tengigabytes/MokyaLora/docs/requirements/hardware-requirements.md

# Hardware Requirements Specification

**Project:** MokyaLora (Project MS-RP2350 — Meshtastic Feature Phone)
**Version:** v5.2

---

## 1. Core Compute

| Role | Part | Package | Notes |
|---|---|---|---|
| MCU | RP2350B | QFN-80 | Dual-core Cortex-M33, 1.8 V logic, no built-in flash |
| Flash | Winbond W25Q128JW | WSON-8 | 16 MB, 1.8 V, QSPI |
| PSRAM | AP Memory APS6404L-3SQN | QFN | 8 MB, 1.8 V, QSPI — holds IME Trie index and UI double-buffer at runtime |
| MCU Crystal | Abracon ABM8-272-T3 | SMD | 12.000 MHz |

**Design constraints:**
- QSPI Flash and PSRAM must be placed adjacent to MCU; 33 Ω series resistors on CLK lines.
- Expose QSPI Flash CS to a test point or micro switch — anti-brick: forces ROM bootloader (UF2 mode).
- Expose SWCLK, SWDIO, GND test points — required for dual-core AMP debugging with a hardware debugger.

---

## 2. Power System

### 2.1 Components

| Role | Part | Package | Notes |
|---|---|---|---|
| Charger / Path | TI BQ25622RYKR | DSBGA-18 | I2C, 16-bit ADC, VINDPM (solar MPPT), OTG 5 V boost; **no D+/D−** to preserve MCU USB signal integrity |
| Buck Inductor | Murata DFE322520F-1R5M | 3225 | 1.5 µH, metal-alloy shielded — lower ripple than 1.0 µH, better for RF-sensitive design |
| Fuel Gauge | TI BQ27441DRZR | SON-12 | Impedance Track™; must be in series with battery current path |
| 1.8 V Buck | TI TPS62840DLCR | VSON-8 | 60 nA Iq — minimises standby current |
| 3.3 V LDO | TI TPS7A2033 | WSON-6 | 300 mA, ultra-low noise (high PSRR) — clean supply for GPS/RF analogue |
| LED / BL Driver | TI LM27965 | WQFN-24 | Dual-bank I2C dimming (Power bus, `i2c1` on RP2350); Bank A = LCD BL, Bank B = keypad BL; HWEN tied to 1.8 V |
| Battery | Nokia BL-4C | — | Li-ion 3.7 V, ~890 mAh |
| Battery Connector | AVX 009155003301006 | 3-pin pogo | 2.5 mm pitch; polarity marked on silkscreen |

### 2.2 Power Rail Summary

| Rail | Voltage | Regulator | Key Loads |
|---|---|---|---|
| 1.8 V | 1.8 V | TPS62840 | MCU, Flash, PSRAM, SX1262 VDD_IN + VBAT_IO, Mic, LCD logic, GPS I/O |
| 3.3 V | 3.3 V | TPS7A2033 | **SX1262 VBAT (PA + Rx)**, GPS RF, LCD analogue, magnetometer, barometer |
| VSYS | ~3.5–4.2 V | BQ25622 | Buck input, LDO input, audio amp, backlight, motor |
| OTG | 5 V | BQ25622 boost | USB VBUS reverse power output |

See `docs/design-notes/power-architecture.md` for the full power tree.

**Design constraints:**
- Charger ILIM: hardware resistor sets 500 mA default; MCU raises limit to 1–2 A via I2C after USB enumeration.
- BQ25622 PMID bulk capacitor must be placed close to IC; VBUS trace rated for ≥ 2 A.
- BQ27441 SRX–VSS sense path must be short and wide (in series with battery current loop).
- TPS7A2033 EN pin tied to VSYS / 1.8 V (always-on).

---

## 3. RF — LoRa

### 3.1 Components

| Role | Part | Package | Notes |
|---|---|---|---|
| LoRa Transceiver | Semtech SX1262 | QFN-24 | SPI1; supports 150–960 MHz sub-GHz bands |
| TCXO | ECS-TXO-20CSMV4-320-AY-TR | SMD | 32 MHz, 1.8 V, ±0.5 ppm, clipped sine output |
| RF Switch | Murata PE4259 | SPDT | Tx / Rx antenna path switching |
| LoRa Antenna | Kyocera AVX M620720 | Chip | Placed at top PCB edge |
| RF Shield | Wurth 3600213120S | SMT frame + lid | Covers digital core to reduce radiated emissions |

### 3.2 SPI1 Interface

| Signal | Notes |
|---|---|
| LORA_MISO  | SPI1 |
| LORA_nCS | SPI1 chip select |
| LORA_SCK | SPI1 |
| LORA_MOSI  | SPI1 |
| LORA_BUSY  | Active-high; poll before each SPI transaction |
| LORA_DIO1  | IRQ / DORMANT wakeup source |
| LORA_nRST  | Active-low reset |

GPIO assignments: see `docs/design-notes/mcu-gpio-allocation.md`.

**Design constraints:**
- RF traces: 50 Ω controlled impedance on dedicated RF layer.
- TCXO XTA pin: 220 Ω series resistor + 10 pF shunt capacitor — mandatory per Semtech application note.
- U.FL test connector on RF signal path for bench RF matching and power verification.

---

## 4. RF — GNSS

### 4.1 Components

| Role | Part | Package | Notes |
|---|---|---|---|
| GNSS Receiver | ST Teseo-LIV3FL | LGA-14 | Multi-constellation; I2C1 (Sensor + GNSS bus), address 0x3A |
| LNA | Infineon BGA123N6 | — | GPS/GNSS LNA; 1.8 V VPON enable |
| SAW Filter | Qualcomm B39162B4327P810 | — | L1 bandpass, after LNA |
| GNSS Antenna | Kyocera AVX M830120 | Chip | Placed at left PCB edge |

**Design constraints:**
- Protocol Select pin must be configured for I2C mode.
- RF trace: 50 Ω controlled impedance.
- 3.3 V supply (TPS7A2033) for RF and analogue sections.
- SDA/SCL share sensor bus pull-ups with other sensors.
- **MCU interface is I2C only** — Teseo `nRST` is **not** routed to any MCU GPIO on Rev A. Firmware can only issue software reset via `$PSTMCOLDSTART` / `$PSTMSRR` proprietary commands over I2C; a hard reset requires power cycling the 3.3 V rail.

---

## 5. Display

### 5.1 Components

| Role | Part | Package | Notes |
|---|---|---|---|
| LCD | Newhaven NHD-2.4-240320AF | — | 2.4″ IPS, 240×320, 8-bit parallel 8080, no touch |
| FPC Connector | Molex 54132-4062 | FPC-40 | 0.5 mm pitch ZIF, 40-pin |

### 5.2 Interface

| Signal | Notes |
|---|---|
| TFT_nCS | Chip select |
| TFT_DCX | Data / command select |
| TFT_nWR | Write strobe |
| TFT_D8–D15 | 8-bit parallel data bus (PIO) |
| TFT_nRST | Reset |
| TFT_TE | Tearing effect |
| Backlight  | LM27965 Bank A, Power-bus I2C dimming |

GPIO assignments: see `docs/design-notes/mcu-gpio-allocation.md`.

**Design constraints:**
- FPC connector: insert FPC with contacts facing **down**; verify orientation before locking ZIF.

---

## 6. Audio

### 6.1 Components

| Role | Part | Package | Notes |
|---|---|---|---|
| Microphone | Infineon IM69D130 | LGA-5 | PDM, SNR 69 dB, AOP 128 dBSPL; bottom-port |
| Audio Amplifier | Nuvoton NAU8315YG | WSON-6 | 3.2 W Class-D I2S |
| Speaker | CUI CMS-131304-SMT-TR | SMT | 0.7 W, 8 Ω |

### 6.2 Interface

| Signal | Notes |
|---|---|
| MIC_CLK  | PDM clock output to mic |
| MIC_DATA | PDM data input from mic |
| AMP_BCLK | I2S bit clock to amp |
| AMP_FSR  | I2S frame sync to amp |
| AMP_DAC  | I2S data output to amp |

GPIO assignments: see `docs/design-notes/mcu-gpio-allocation.md`.

**Design constraints:**
- IM69D130 is a bottom-port microphone: PCB must have an acoustic opening aligned to the mic inlet; enclosure must seal the acoustic cavity with a rubber gasket.
- NAU8315 software must limit output to −3 dB to protect the speaker from over-drive.

---

## 7. Sensors

### 7.1 Components

| Role | Part | Package | I2C1 Address | Address Setting |
|---|---|---|---|---|
| IMU (ACC + GYRO) | ST LSM6DSV16X | LGA-14 | 0x6A | SA0 → GND (default 0x6B conflicts with charger on the other bus) |
| Magnetometer | ST LIS2MDL | LGA-12 | 0x1E | Fixed |
| Barometer | ST LPS22HH | LGA-10 | 0x5D | SA0 → 3.3 V (Rev A confirmed; schematic ties SA0 to 3.3 V) |

All sensors share the **sensor + GNSS bus (GPIO 34 / 35)** with the Teseo-LIV3FL GNSS receiver. The Power bus (GPIO 6 / 7) and the Sensor + GNSS bus both map to the `i2c1` SDK peripheral on RP2350 (no I2C0 pinmux alternative exists on either pin pair); Rev A firmware time-multiplexes `i2c1` between the two pin pairs via a FreeRTOS mutex. Rev B should reroute the sensor + GNSS bus to a mod-4 = 0/1 GPIO pair to restore two independent SDK peripherals — see `docs/design-notes/mcu-gpio-allocation.md` for details.

**Design constraints:**
- LSM6DSV16X SA0 must be tied to GND — default address 0x6B would collide with BQ25622 if both were on the same bus.
- LPS22HH SA0 is tied to 3.3 V → address 0x5D (confirmed Rev A bring-up).
- I2C1 pull-ups: 2.2 kΩ–4.7 kΩ to 1.8 V on SDA and SCL.

---

## 8. Human Interface

### 8.1 Keypad

| Role | Part | Notes |
|---|---|---|
| Keypad Switches | SWT0105 | Metal dome sheet |
| Anti-ghost Diodes | Diodes Inc. SDM03U40 | SOD-523 Schottky, Vf ~0.37 V @ 30 mA; enables NKRO at 1.8 V logic |
| Keypad BL LEDs | LiteOn LTST-C191TBWET (×6–8) | White; driven by LM27965 Bank B (Power bus, `i2c1` on RP2350) |

**Scan mechanism:** RP2350 PIO drives 6 column lines, samples 6 row lines. DMA writes key state directly to RAM — zero CPU overhead. Logic level 1.8 V, active-low. GPIO assignments: see `docs/design-notes/mcu-gpio-allocation.md`.

#### Physical Layout (6×6 Matrix)

```
[ Navigation & Control Area ]

      (Left)        (D-Pad)        (Right)      (Vol)
    +--------+    +    +    +    +--------+  +--------+
    |  FUNC  |    |    ▲    |    |   SET  |  |  VOL+  |
    +--------+    +    |    +    +--------+  +--------+
                  +--+ | +--+
             ◄ -- |  | OK |  | -- ►
                  +--+ | +--+
    +--------+    +    |    +    +--------+  +--------+
    |  BACK  |    |    ▼    |    |   DEL  |  |  VOL-  |
    +--------+    +    +    +    +--------+  +--------+

[ Core Input Area (5×5) ]

       Col 0       Col 1       Col 2       Col 3       Col 4
    +-------+   +-------+   +-------+   +-------+   +-------+
 R0 | 1 2   |   | 3 4   |   | 5 6   |   | 7 8   |   | 9 0   |
    | ㄅㄉ  |   | ˇˋ    |   | ㄓˊ   |   | ˙ㄚ   |   | ㄞㄢㄦ |
    | [ANS] |   | [7]   |   | [8]   |   | [9]   |   | [÷]   |
    +-------+   +-------+   +-------+   +-------+   +-------+
 R1 | Q W   |   | E R   |   | T Y   |   | U I   |   | O P   |
    | ㄆㄊ  |   | ㄍㄐ  |   | ㄔㄗ  |   | ㄧㄛ  |   | ㄟㄣ  |
    | [(]   |   | [4]   |   | [5]   |   | [6]   |   | [×]   |
    +-------+   +-------+   +-------+   +-------+   +-------+
 R2 | A S   |   | D F   |   | G H   |   | J K   |   |   L   |
    | ㄇㄋ  |   | ㄎㄑ  |   | ㄕㄘ  |   | ㄨㄜ  |   | ㄠㄤ  |
    | [)]   |   | [1]   |   | [2]   |   | [3]   |   | [-]   |
    +-------+   +-------+   +-------+   +-------+   +-------+
 R3 | Z X   |   | C V   |   | B N   |   |   M   |   |  ---  |
    | ㄈㄌ  |   | ㄏㄒ  |   | ㄖㄙ  |   | ㄩㄝ  |   | ㄡㄥ  |
    | [AC]  |   | [0]   |   | [.]   |   | [x10ˣ]|   | [+]   |
    +-------+   +-------+   +-------+   +-------+   +-------+
 R4 | MODE  |   |  TAB  |   | SPACE |   | ，SYM |   | 。.？ |
    +-------+   +-------+   +-------+   +-------+   +-------+
```

#### Electrical Matrix Map

| Row \ Col | Col 0 | Col 1 | Col 2 | Col 3 | Col 4 | Col 5 (ext) |
|---|---|---|---|---|---|---|
| Row 0 | 1 2 / ㄅㄉ / ANS | 3 4 / ˇˋ / 7 | 5 6 / ㄓˊ / 8 | 7 8 / ˙ㄚ / 9 | 9 0 / ㄞㄢ / ÷ | FUNC |
| Row 1 | Q W / ㄆㄊ / ( | E R / ㄍㄐ / 4 | T Y / ㄔㄗ / 5 | U I / ㄧㄛ / 6 | O P / ㄟㄣ / × | SET |
| Row 2 | A S / ㄇㄋ / ) | D F / ㄎㄑ / 1 | G H / ㄕㄘ / 2 | J K / ㄨㄜ / 3 | L / ㄠㄤ / - | BACK |
| Row 3 | Z X / ㄈㄌ / AC | C V / ㄏㄒ / 0 | B N / ㄖㄙ / . | M / ㄩㄝ / x10ˣ | — / ㄡㄥ / + | DEL |
| Row 4 | MODE | TAB | SPACE | ，SYM | 。.？ | VOL+ |
| Row 5 (nav) | UP | DOWN | LEFT | RIGHT | OK | VOL− |

> **Rev A bringup note:** The schematic SW designators are numbered column-major (SW1–6 = logical Col 5 ext top-to-bottom, i.e. FUNC/SET/BACK/DEL/VOL+/VOL−, then SW7–12 = Col 0 number row, etc.). As a result, the firmware GPIO scan index `(r, c)` does **not** correspond to the logical Row/Col above. See `docs/bringup/rev-a-bringup-log.md` Step 6 for the confirmed firmware `key_names[r][c]` table. Correct SW-to-Row/Col assignment should be verified against the schematic before Rev B firmware development.

### 8.2 Indicators & Haptics

| Role | Part | Notes |
|---|---|---|
| Status LED | LiteOn LTST-C235KGKRKT | Side-view, red/green; driven via LM27965 remaining channels; 256-step I2C dimming |
| Vibration Motor | HD-EMB1104-SM-2 | SMD ERM, 3 V, 80 mA |
| Motor MOSFET | Toshiba SSM3K56ACT | N-ch, low Vth, 1.8 V logic compatible, CST3; low-side driver |
| Motor Protection | Flyback diode | Reverse-parallel across motor terminals to absorb back-EMF |

**Design constraints:**
- 1.8 V GPIO rule: never drive LEDs or high-Vth MOSFETs directly from GPIO. Use SSM3K56ACT (low-Vth).
  - LED: common-anode to VSYS / 3.3 V; cathode through resistor to Drain; 100 kΩ pull-down on Gate.
  - Motor: low-side drive; motor+ to VSYS (5–10 Ω series); motor− to Drain.
- Flyback diode reverse-parallel across motor terminals is mandatory.

---

## 9. Connectivity — USB-C

| Role | Part | Package | Notes |
|---|---|---|---|
| USB-C Connector | GCT USB4105-GF-A | 16-pin mid-mount | Through-hole shell legs must be soldered for mechanical retention |

**Design constraints:**
- CC1 and CC2 must each have an **independent** 5.1 kΩ pull-down to GND — enables PD charger 5 V output.
- D+/D− connected to MCU only — not to charger IC (preserves USB signal integrity).
- ESD protection devices on D+/D− and VBUS.
- VBUS trace rated for ≥ 2 A.

---

## 10. I2C Bus Allocation

Bus assignments, 7-bit addresses, GPIO pin pairs, pull-up values, and the
RP2350 SDK peripheral note all live in
`docs/design-notes/mcu-gpio-allocation.md` to keep a single source of truth.

---

## 11. Mandatory Design Rules

1. **Anti-brick boot point:** expose QSPI Flash CS to a test point or micro switch — allows ROM bootloader entry when software is bricked.
2. **SWD debug interface:** expose SWCLK, SWDIO, GND — required for dual-core AMP debugging.
3. **1.8 V GPIO rule:** never drive LEDs or high-Vth MOSFETs directly. Use SSM3K56ACT (low-Vth) as switch.
   - LED: common-anode to VSYS / 3.3 V; cathode through resistor to Drain; 100 kΩ pull-down on Gate.
   - Motor: low-side drive; motor+ to VSYS (5–10 Ω series); motor− to Drain.
4. **OTG wiring:** BQ25622 PMID bulk capacitor must be close to IC; VBUS trace rated for ≥ 2 A.
5. **Fuel gauge path:** BQ27441 SRX–VSS sense path in battery current loop; trace must be short and wide.
6. **Acoustic seal:** IM69D130 is bottom-port; PCB must have an opening aligned to mic inlet; enclosure must seal with a rubber gasket.
7. **Signal integrity:** QSPI CLK lines need 33 Ω series resistors; Flash and PSRAM placed adjacent to MCU.
8. **Motor protection:** flyback diode reverse-parallel across motor terminals is mandatory.
9. **GPS I2C mode:** Teseo-LIV3FL Protocol Select pin must be configured for I2C mode.
10. **USB-C CC pins:** CC1 and CC2 must each have an independent 5.1 kΩ pull-down to GND to enable PD charger 5 V output.

---

## 12. Rev B Changes (Planned)

Changes based on Rev A bringup findings:

| Change | Reason | Priority | Reference |
|---|---|---|---|
| **TPS7A2033 EN → GPIO** | Gate 3.3 V rail in deepest DORMANT (PWR_BTN only, no LoRa) | **Critical** | Power review §8.4 |
| **Load switch on non-LoRa 3.3 V loads** | Isolate Teseo/LCD/sensors from SX1262 VBAT in STANDBY; SX1262 VBAT stays powered | **High** | Power review §8.4 |
| **Add NAND Flash** | Non-volatile storage (maps, message DB, OTA) | **High** | New requirement |
| **Remove NAU8315 amp + CMS-131304 speaker** | Audio not needed | High | User decision |
| **Remove IM69D130 PDM mic** | Audio not needed | High | User decision |
| **LM27965 HWEN → GPIO** | Full LED driver shutdown in DORMANT; saves ~5 µA | Medium | Power review §8.4 |
| Fix LIS2MDL I2C routing (SCL/SDA swap) | Issue 3 | High | Bringup log |
| Fix LPS22HH I2C routing + SA0 net | Issue 4 | High | Bringup log |
| Fix LCD FPC pinout | Issue 5 | High | Bringup log |
| Move D37 LED to LM27965 Bank A | Issue 6 | Medium | Bringup log |
| BQ25622 nCE → GND | Issue 2 | High | Bringup log |
| PSRAM GPIO 0 pull-up (4.7–10 kΩ) | Issue 8 | Medium | Bringup log |
| Consider I2C Bus B pull-up load switch | Protect against BQ27441 latchup drain (Issue 10) | Low | Power review §8.4 |

### NAND Flash (TBD)

- **Part:** TBD — select SPI NAND for minimal GPIO usage (shares SPI bus or dedicated CS)
- **Interface:** SPI or QSPI
- **Capacity:** TBD (512 MB–2 GB range typical for maps + message DB)
- **Power:** verify standby current; must support CE# deassert or Deep Power Down for low-power mode
- **Use cases:** offline vector maps, message history database, firmware OTA staging, large asset storage
- **Flash memory map impact:** LittleFS partition on NOR Flash (W25Q128JW) may be reduced or eliminated if NAND takes over user data storage; NOR retains firmware + MIE dictionary
