tengigabytes/MokyaLora/docs/bringup/mie-v4-status.md

# MIE v4 Composition Architecture — Status

Last updated: 2026-04-24

## Overview

The MokyaInput Engine has been refactored to **v4 Composition Architecture** to
solve three independent problems found via SWD+RTT latency profiling:

1. **Performance**: v2 `TrieSearcher::search` did O(words × 50) dedup linear
   scan over PSRAM — 580 ms worst case for common Bopomofo initials (ㄅ ㄉ).
2. **Coverage**: v2 dict had only 1,479 single chars reachable as 1-syllable
   IME input; users couldn't type many CJK chars.
3. **Ranking**: Same dict held all word lengths competing by freq, so 4-char
   成語 were perpetually ranked below higher-freq 2-char compounds.

## Architecture (one-paragraph summary)

A single `dict_mie.bin` (MIE4 magic) holds:
- `char_table`: 18,722 unique chars × per-char readings (key bytes + tone + freq)
- `word_table`: 128,855 multi-char words as `char_id[N]` sequences with
  per-position `reading_idx[N]` overrides for 多音字
- `first_char_idx`: per char_id → freq-sorted word_id list
- `key_to_char_idx`: per phoneme-key byte → candidate char_ids
- `char_offsets` / `word_offsets`: pre-computed u32 offsets into char_table /
  word_table (zero-heap embedded loader)

`CompositionSearcher::search(user_keys, n, target_char_count, ...)` walks
`key_to_char_idx[user_keys[0]]` → candidate chars → `first_char_idx[cid]` →
word_ids → `composition_matches` recursive backtracker over each char's
designated reading. **No abbreviation pre-computation in the dict** — search-
time composition derives all valid prefix patterns from char readings.

`ImeLogic::run_search_v4()` dispatches by `count_positions(key_seq_)`:
- 1-position → `search_chars` (char_table, not word_table group 1)
- 2-4 position → `target_char_count = positions` + adjacent-bucket fallback
- 5+ position → **char-by-char mode**: 1-char candidates for first initial
  (commit consumes 1 byte) + appended 5+ phrase matches as bonus

## Completed (Phase 0-5, Phase 1.4 A/B/C)

| Phase | Item | Status |
|---|---|---|
| 1.4 A | Long-press multitap cycling (short=fuzzy, long×N = primary/secondary/tertiary, mod phoneme_count) | ✅ 2026-04-24 |
| 1.4 A | Dict phoneme_pos byte (+1 % size) + `CompositionSearcher` hint filter | ✅ |
| 1.4 A | Engine `lp_cycle_` FSM + KeyEvent.flags + keypad_scan deferred press + 2-byte inject ring | ✅ |
| 1.4 B | SYM1 long-press 4×4 symbol picker (「」『』（）【】，。、；：？！…) | ✅ 2026-04-24 |
| 1.4 C | Idle OK = newline (mirrors idle SPACE = " ") | ✅ 2026-04-24 |
| 1.4 | 150 host unit tests green | ✅ |
| 1.4 | 6-passage SWD regression: 1 416 CJK / 100 % top-100 / 0 miss + 136/136 picker punct + 21/21 newlines + 48/48 spaces | ✅ |
| 0 | PoC simulation script (`scripts/poc_mie_v4_simulation.py`) | ✅ |
| 0 | Validation: dict ≤ 2.5 MB, ref-search p50 ≤ 5 ms | ✅ |
| 1 | `gen_dict.py` MIED v4 builder (parallel `--v4-output` flag) | ✅ |
| 1 | v4 binary format with embedded offset sections | ✅ |
| 1 | `verify_mied_v4.py` round-trip parser | ✅ |
| 2 | `CompositionSearcher` C++ class (header + impl + 8 tests) | ✅ |
| 2 | Backtracking `composition_matches` for abbreviation derivation | ✅ |
| 2 | `search_chars` for 1-char results from char_table | ✅ |
| 2 | Heap-free embedded loader (offsets read from file, not built) | ✅ |
| 3 | Position counter (H2 heuristic) in `ime_keys.cpp` | ✅ |
| 3 | `ImeLogic::run_search_v4` with bucket dispatch + fallback chains | ✅ |
| 3 | 5+ char-by-char mode | ✅ |
| 3 | `attach_composition_searcher` API (back-compat with v2 path) | ✅ |
| 4 | `test_position_counter.cpp` (16 tests) | ✅ |
| 4 | `test_composition_searcher.cpp` (8 tests) | ✅ |
| 4 | `test_ime_v4_dispatch.cpp` (4 tests incl. real-dict smoke) | ✅ |
| 4 | All 123 PC tests green | ✅ |
| 5 | `mie_dict_loader.c` v4 magic auto-detection + load path | ✅ |
| 5 | `ime_task.cpp` conditional CompositionSearcher attach | ✅ |
| 5 | `scripts/build_and_flash.sh --v4` flag | ✅ |
| 5 | Hardware boot + RTT measurement (initial run) | ✅ |
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
