tengigabytes/MokyaLora/hardware/kicad/BtryChrgr.kicad_sch

## KiCad design hardware/kicad/BtryChrgr.kicad_sch (2026-03-22)

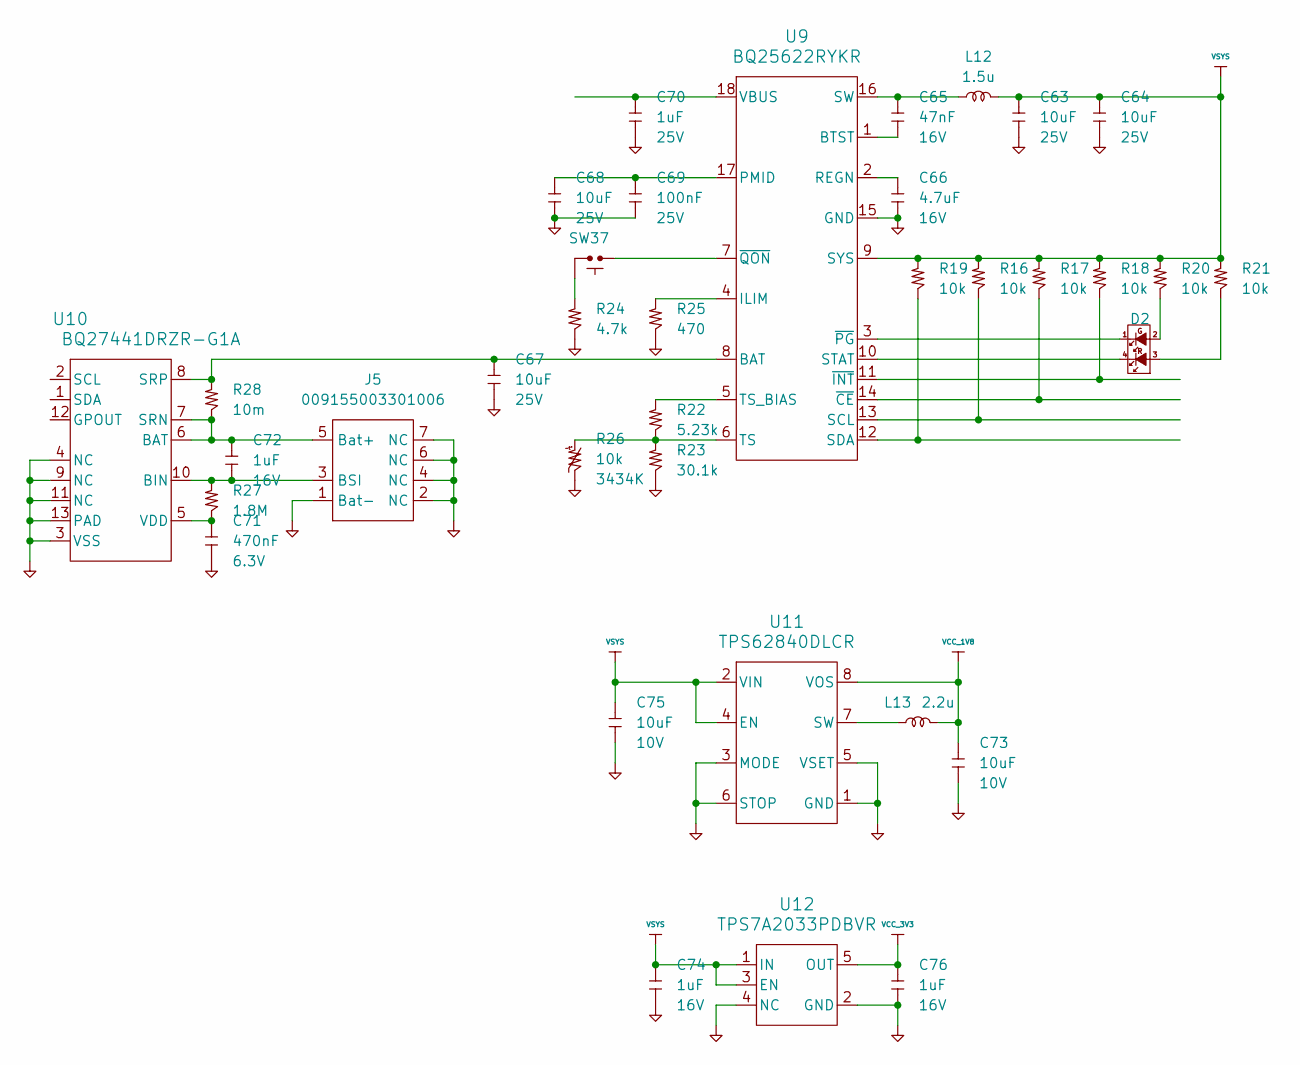
[picture p15: schematic BtryChrgr.kicad_sch]

Parts:
C63, C64, C67, C68: 10uF; C_1206_3216; Voltage 25V; MPN CC1206KKX7R8BB106
C65: 47nF; C_0402_1005; Voltage 16V; MPN AC0402KPX7R7BB473
C66: 4.7uF; C_0805_2012; Voltage 16V; MPN AC0805KKX7R7BB475
C69: 100nF; C_0402_1005; Voltage 25V; MPN AC0402KRX7R8BB104
C70: 1uF; C_1206_3216; Voltage 25V; MPN CC1206JKX7R8BB105
C71: 470nF; C_0402_1005; Voltage 6.3V; MPN AC0402KRX5R5BB474
C72, C74, C76: 1uF; C_0603_1608; Voltage 16V; MPN AC0603KRX7R7BB105
C73, C75: 10uF; C_0603_1608; Voltage 10V; MPN CC0603KRX5R6BB106
D2: LTST-C235KGKRKT; LED_LiteOn_LTST-C235KGKRKT
J5: 009155003301006; Mouser Part Number 581-009155003301006
L12: 1.5u; L_1210_3225; MPN DFE322520F-1R5M
L13: 2.2u; L_0806_2016; MPN DFE201612E-2R2M=P2
R16, R17, R18, R19, R20, R21: 10k; R_0402_1005; MPN AC0402FR-7W10KL
R22: 5.23k; R_0402_1005; MPN AC0402FR-075K23L
R23: 30.1k; R_0402_1005; MPN AC0402FR-0730K1L
R24: 4.7k; R_0402_1005; MPN AC0402FR-7W4K7L
R25: 470; R_0402_1005; MPN AC0402FR-7W470RL
R26: 10k; R_0402_1005; MPN NCU15XH103FBSRC
R27: 1.8M; R_0402_1005; MPN AC0402FR-071M8L
R28: 10m; R_0805_2012; MPN PA0805FRE470R01L
SW37: SWT0105-003516JSA; SWT0105
U9: BQ25622RYKR; WQFN-HR18__RYK_TEX; MPN BQ25622RYKR
U10: BQ27441DRZR-G1A; DRZ0012A
U11: TPS62840DLCR; VSON8_2P1X1P6_TEX
U12: TPS7A2033PDBVR; DBV0005A-IPC_C; MPN TPS7A2033PDBVR

Connections:
GND: C63.2, C64.2, C66.2, C67.2, C68.2, C69.2, C70.2, C71.2, C73.2, C74.2, C75.2, C76.2, J5.1 (Bat-), J5.2 (NC), J5.4 (NC), J5.6 (NC), J5.7 (NC), R23.2, R24.2, R25.2, R26.2, U9.15 (GND), U10.3 (VSS), U10.4 (NC), U10.9 (NC), U10.11 (NC), U10.13 (PAD), U11.1 (GND), U11.3 (MODE), U11.5 (VSET), U11.6 (STOP), U12.2 (GND), U12.4 (NC)
unnamed: C65.1, L12.1, U9.16 (SW)
unnamed: C65.2, U9.1 (BTST)
unnamed: C66.1, U9.2 (REGN)
unnamed: C67.1, R28.1, U9.8 (BAT), U10.8 (SRP)
unnamed: C68.1, C69.1, U9.17 (PMID)
unnamed: C70.1, U9.18 (VBUS)
unnamed: C71.1, R27.2, U10.5 (VDD)
unnamed: C72.1, J5.5 (Bat+), R28.2, U10.6 (BAT), U10.7 (SRN)
unnamed: C72.2, J5.3 (BSI), R27.1, U10.10 (BIN)
unnamed: D2.1 (K2), U9.3 (~PG)
unnamed: D2.2 (A2), R20.2
unnamed: D2.3 (A1), R21.2
unnamed: D2.4 (K1), U9.10 (STAT)
unnamed: L13.1, U11.7 (SW)
unnamed: R16.2, U9.13 (SCL)
unnamed: R17.2, U9.14 (~CE)
unnamed: R18.2, U9.11 (~INT)
unnamed: R19.2, U9.12 (SDA)
unnamed: R22.1, U9.5 (TS_BIAS)
unnamed: R22.2, R23.1, R26.1, U9.6 (TS)
unnamed: R24.1, SW37.1, SW37.2
unnamed: R25.1, U9.4 (ILIM)
unnamed: SW37.3, SW37.4, U9.7 (~QON)
VCC_1V8: C73.1, L13.2, U11.8 (VOS)
VCC_3V3: C76.1, U12.5 (OUT)
VSYS: C63.1, C64.1, C74.1, C75.1, L12.2, R16.1, R17.1, R18.1, R19.1, R20.1, R21.1, U9.9 (SYS), U11.2 (VIN), U11.4 (EN), U12.1 (IN), U12.3 (EN)
