tengigabytes/MokyaLora/hardware/kicad/Display.kicad_sch

## KiCad design hardware/kicad/Display.kicad_sch (2026-04-07)

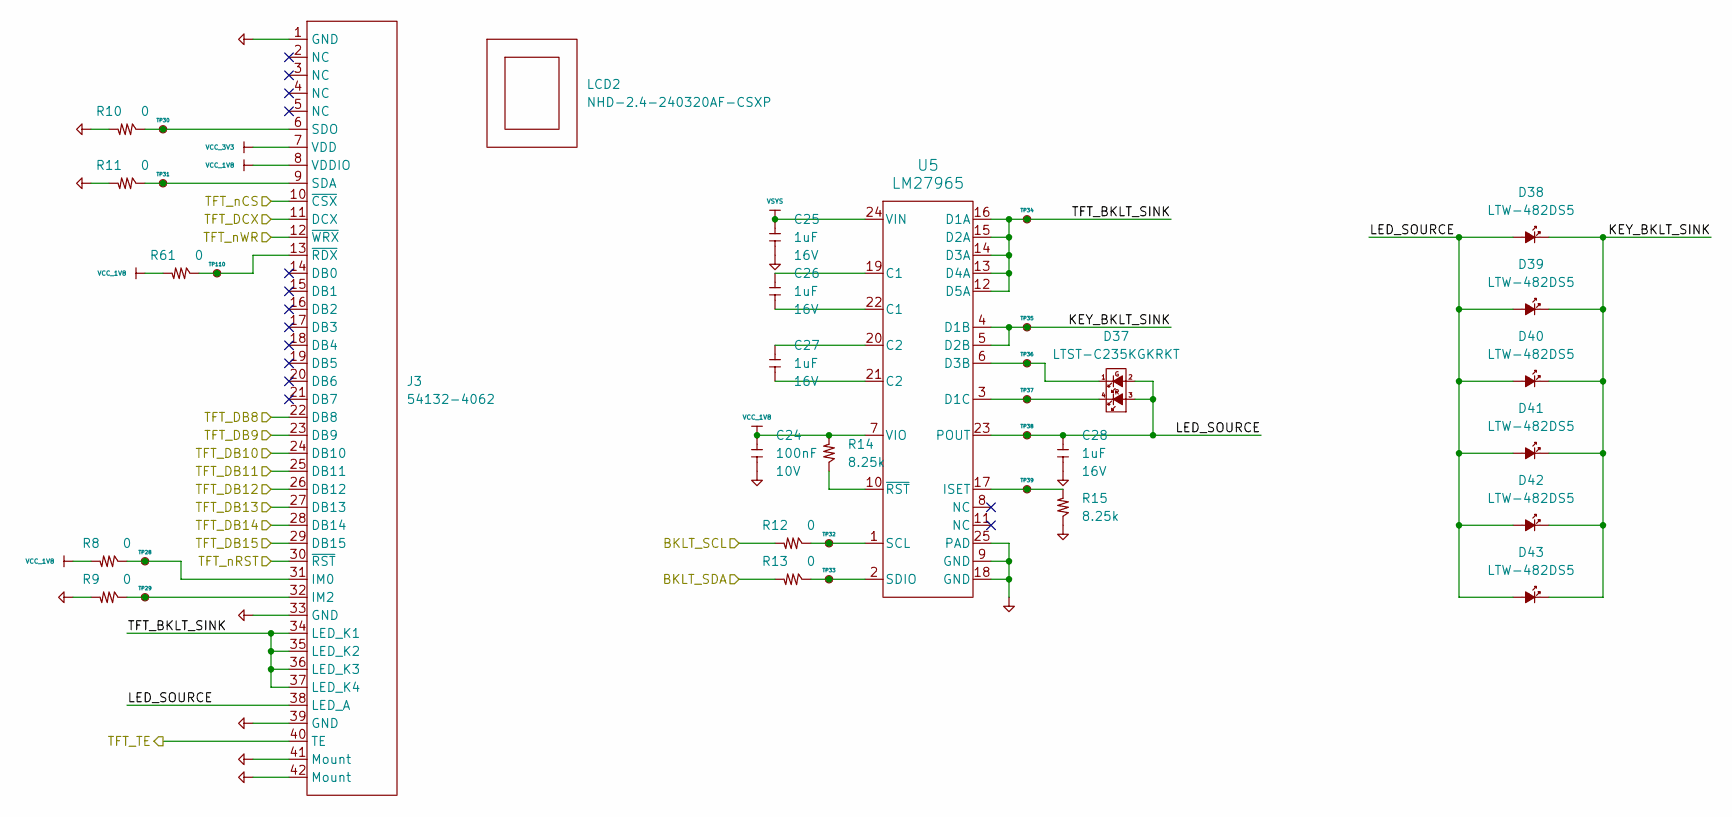
[picture p16: schematic Display.kicad_sch]

Parts:
C24: 100nF; C_0402_1005; Voltage 10V; MPN AC0402KRX7R6BB104; LCSC C3830899
C25, C26, C27, C28: 1uF; C_0603_1608; Voltage 16V; MPN AC0603KRX7R7BB105; LCSC C3905328
D37: LTST-C235KGKRKT; LED_LiteOn_LTST-C235KGKRKT; MPN LTST-C235KGKRKT; LCSC C125110
D38, D39, D40, D41, D42, D43: LTW-482DS5; MPN LTW-482DS5; LCSC C284930
J3: 54132-4062; 54132-4062_1; Mouser Part Number 538-54132-4062
LCD2: NHD-2.4-240320AF-CSXP; MPN NHD-2.4-240320AF-CSXP
R8, R9, R10, R11, R12, R13, R61: 0; R_0402_1005; MPN AC0402FR-070RL; LCSC C226739
R14, R15: 8.25k; R_0402_1005; MPN AC0402FR-078K25L; LCSC C227259
TP28, TP29, TP30, TP31, TP32, TP33, TP34, TP35, TP36, TP37, TP38, TP39, TP110: TestPoint_Small; TestPoint_Pad_D1.0mm; MPN test point
U5: LM27965; SQA24A; MPN LM27965SQ; LCSC C2679390

Connections:
BKLT_SCL: R12.1
BKLT_SDA: R13.1
GND: C24.2, C25.2, C28.2, J3.1 (GND), J3.33 (GND), J3.39 (GND), J3.41 (Mount), J3.42 (Mount), R9.1, R10.1, R11.1, R15.2, U5.9 (GND), U5.18 (GND), U5.25 (PAD)
KEY_BKLT_SINK: D38.C, D39.C, D40.C, D41.C, D42.C, D43.C, TP35.1, U5.4 (D1B), U5.5 (D2B)
LED_SOURCE: C28.1, D37.2 (A2), D37.3 (A1), D38.A, D39.A, D40.A, D41.A, D42.A, D43.A, J3.38 (LED_A), TP38.1, U5.23 (POUT)
unnamed: C26.1, U5.19 (C1)
unnamed: C26.2, U5.22 (C1)
unnamed: C27.1, U5.20 (C2)
unnamed: C27.2, U5.21 (C2)
unnamed: D37.1 (K2), TP36.1, U5.6 (D3B)
unnamed: D37.4 (K1), TP37.1, U5.3 (D1C)
unnamed: J3.6 (SDO), R10.2, TP30.1
unnamed: J3.9 (SDA), R11.2, TP31.1
unnamed: J3.13 (~RDX), R61.2, TP110.1
unnamed: J3.31 (IM0), R8.2, TP28.1
unnamed: J3.32 (IM2), R9.2, TP29.1
unnamed: R12.2, TP32.1, U5.1 (SCL)
unnamed: R13.2, TP33.1, U5.2 (SDIO)
unnamed: R14.2, U5.10 (~RST)
unnamed: R15.1, TP39.1, U5.17 (ISET)
TFT_BKLT_SINK: J3.34 (LED_K1), J3.35 (LED_K2), J3.36 (LED_K3), J3.37 (LED_K4), TP34.1, U5.12 (D5A), U5.13 (D4A), U5.14 (D3A), U5.15 (D2A), U5.16 (D1A)
TFT_DB8: J3.22 (DB8)
TFT_DB9: J3.23 (DB9)
TFT_DB10: J3.24 (DB10)
TFT_DB11: J3.25 (DB11)
TFT_DB12: J3.26 (DB12)
TFT_DB13: J3.27 (DB13)
TFT_DB14: J3.28 (DB14)
TFT_DB15: J3.29 (DB15)
TFT_DCX: J3.11 (DCX)
TFT_TE: J3.40 (TE)
TFT_nCS: J3.10 (~CSX)
TFT_nRST: J3.30 (~RST)
TFT_nWR: J3.12 (~WRX)
VCC_1V8: C24.1, J3.8 (VDDIO), R8.1, R14.1, R61.1, U5.7 (VIO)
VCC_3V3: J3.7 (VDD)
VSYS: C25.1, U5.24 (VIN)
