tengigabytes/MokyaLora/hardware/kicad/GNSS.kicad_sch

## KiCad design hardware/kicad/GNSS.kicad_sch (2026-04-07)

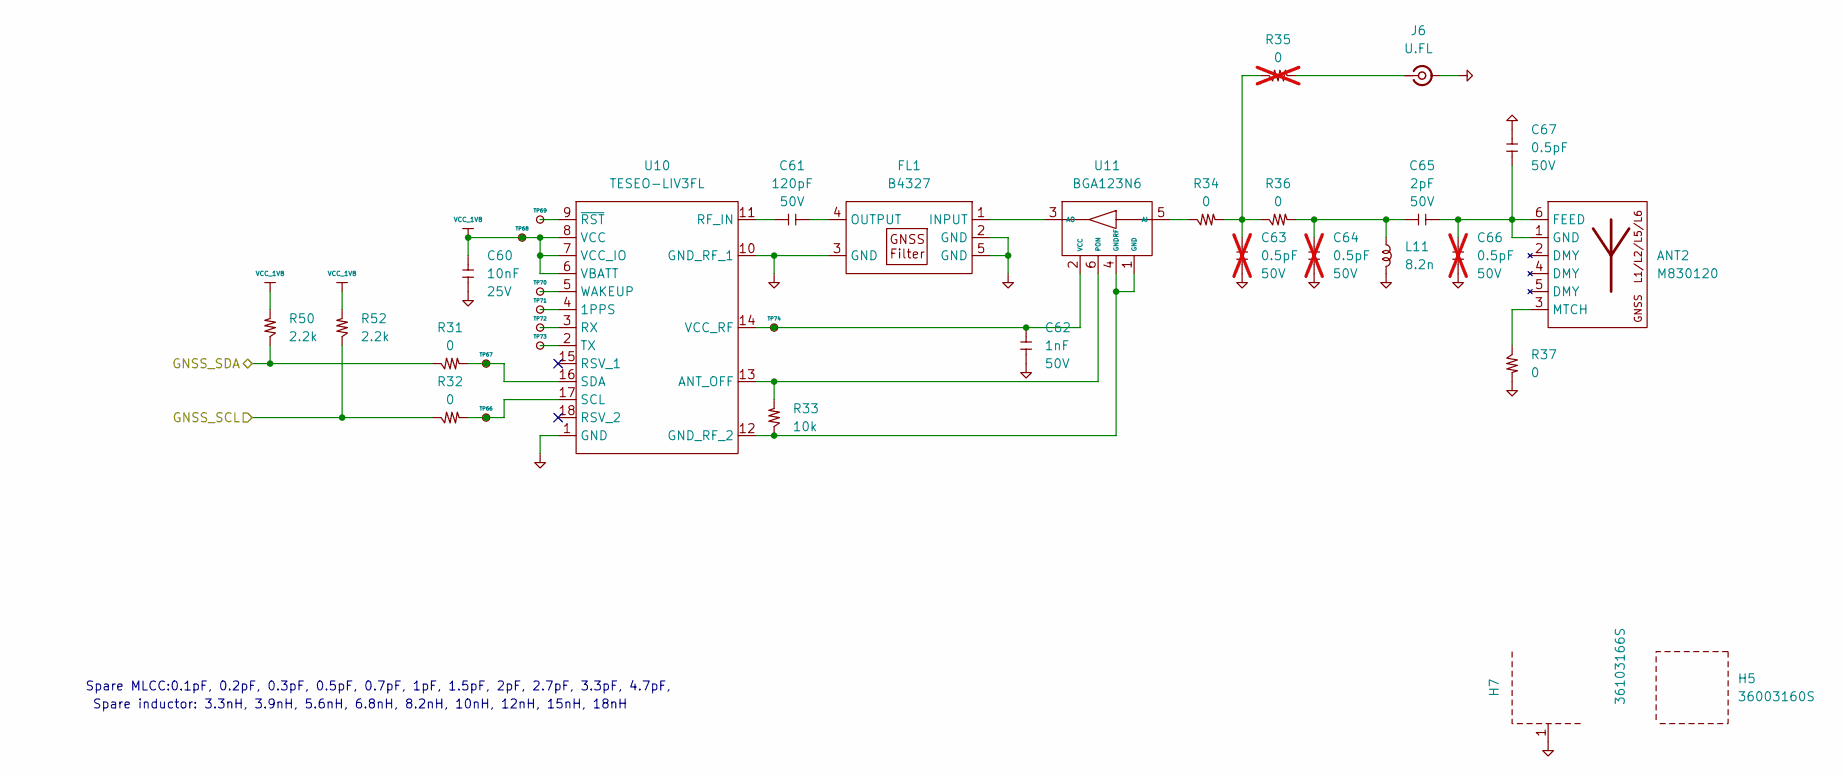
[picture p17: schematic GNSS.kicad_sch]

Parts:
ANT2: M830120; SON225P300X800X143-6N; Mouser Part Number 581-M830120
C60: 10nF; C_0402_1005; Voltage 25V; MPN AC0402KRX7R8BB103; LCSC C726521
C61: 120pF; C_0402_1005; Voltage 50V; MPN AC0402FRNPO9BN121; LCSC C6117687
C62: 1nF; C_0402_1005; Voltage 50V; MPN AC0402JRX7R9BB102; LCSC C726132
C63, C64, C66: 0.5pF; C_0402_1005; Voltage 50V; MPN AC0402BRNPO9BNR50; LCSC C2188174; not fitted
C65: 2pF; C_0402_1005; Voltage 50V; MPN AC0402BRNPO9BN2R0; LCSC C726106
C67: 0.5pF; C_0402_1005; Voltage 50V; MPN AC0402BRNPO9BNR50; LCSC C2188174
FL1: B4327; B39162B4327P810; Mouser Part Number 871-B39162B4327P810
H5: 36003160S; MPN 36003160S
H7: 36103166S; Part Number 36103166S; LCSC C7464147
J6: U.FL; U.FL_Hirose_U.FL-R-SMT-1_Vertical; MPN U.FL-R-SMT-1; LCSC C88374
L11: 8.2n; L_0402_1005; MPN LQW15AN8N2G80D; LCSC C307610
R31, R32, R34, R36, R37: 0; R_0402_1005; MPN AC0402FR-070RL; LCSC C226739
R33: 10k; R_0402_1005; MPN AC0402FR-7W10KL; LCSC C850723
R35: 0; R_0402_1005; MPN AC0402FR-070RL; LCSC C226739; not fitted
R50, R52: 2.2k; R_0402_1005; MPN AC0402FR-072K2L
TP66, TP67, TP68, TP69, TP70, TP71, TP72, TP73, TP74: TestPoint_Small; TestPoint_Pad_D1.0mm; MPN test point
U10: TESEO-LIV3FL; TESEOLIV3FL; Mouser Part Number 511-TESEO-LIV3FL
U11: BGA123N6; BGA725L6E6327; MPN BGA123N6E6327XTSA1; LCSC C3191830

Connections:
GND: C60.2, C62.2, C63.2, C64.2, C66.2, C67.1, FL1.2 (GND), FL1.3 (GND), FL1.5 (GND), H7.1, J6.2 (Ext), L11.2, R37.1, U10.1 (GND), U10.10 (GND_RF_1)
GNSS_SCL: R32.2, R52.2
GNSS_SDA: R31.2, R50.2
unnamed: ANT2.1 (GND), ANT2.6 (FEED), C65.2, C66.1, C67.2
unnamed: ANT2.3 (MTCH), R37.2
unnamed: C61.1, U10.11 (RF_IN)
unnamed: C61.2, FL1.4 (OUTPUT)
unnamed: C62.1, TP74.1, U10.14 (VCC_RF), U11.2 (VCC)
unnamed: C63.1, R34.1, R35.2, R36.2
unnamed: C64.1, C65.1, L11.1, R36.1
unnamed: FL1.1 (INPUT), U11.3 (AO)
unnamed: J6.1 (In), R35.1
unnamed: R31.1, TP67.1, U10.16 (SDA)
unnamed: R32.1, TP66.1, U10.17 (SCL)
unnamed: R33.1, U10.13 (ANT_OFF), U11.6 (PON)
unnamed: R33.2, U10.12 (GND_RF_2), U11.1 (GND), U11.4 (GNDRF)
unnamed: R34.2, U11.5 (AI)
unnamed: TP69.1, U10.9 (~RST)
unnamed: TP70.1, U10.5 (WAKEUP)
unnamed: TP71.1, U10.4 (1PPS)
unnamed: TP72.1, U10.3 (RX)
unnamed: TP73.1, U10.2 (TX)
VCC_1V8: C60.1, R50.1, R52.1, TP68.1, U10.6 (VBATT), U10.7 (VCC_IO), U10.8 (VCC)

Notes on the sheet:
Spare inductor: 3.3nH, 3.9nH, 5.6nH, 6.8nH, 8.2nH, 10nH, 12nH, 15nH, 18nH
Spare MLCC:0.1pF, 0.2pF, 0.3pF, 0.5pF, 0.7pF, 1pF, 1.5pF, 2pF, 2.7pF, 3.3pF, 4.7pF,
