tengigabytes/MokyaLora/hardware/kicad/IMU.kicad_sch

## KiCad design hardware/kicad/IMU.kicad_sch (2026-04-07)

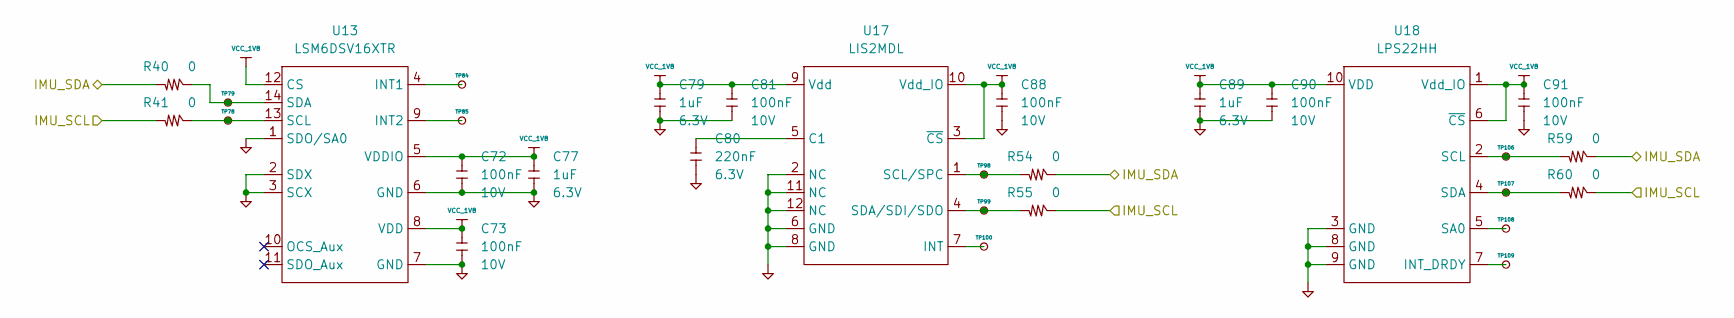
[picture p18: schematic IMU.kicad_sch]

Parts:
C72, C73, C81, C88, C90, C91: 100nF; C_0402_1005; Voltage 10V; MPN AC0402KRX7R6BB104; LCSC C3830899
C77, C79, C89: 1uF; C_0402_1005; Voltage 6.3V; MPN AC0402KRX5R5BB105; LCSC C3873469
C80: 220nF; C_0402_1005; Voltage 6.3V; MPN AC0402KRX5R5BB224; LCSC C3845337
R40, R41, R54, R55, R59, R60: 0; R_0402_1005; MPN AC0402FR-070RL; LCSC C226739
TP78, TP79, TP84, TP85, TP98, TP99, TP100, TP106, TP107, TP108, TP109: TestPoint_Small; TestPoint_Pad_D1.0mm; MPN test point
U13: LSM6DSV16XTR; LGA-14_3x2.5mm_P0.5mm_LayoutBorder3x4y; MPN LSM6DSV16XTR; LCSC C5267406
U17: LIS2MDL; LGA-12_2x2mm_P0.5mm; MPN LIS2MDL; LCSC C919695
U18: LPS22HH; ST_HLGA-10_2x2mm_P0.5mm_LayoutBorder3x2y; MPN LPS22HH; LCSC C2827824

Connections:
GND: C72.2, C73.2, C77.2, C79.2, C80.2, C81.2, C88.2, C89.2, C90.2, C91.2, U13.1 (SDO/SA0), U13.2 (SDX), U13.3 (SCX), U13.6 (GND), U13.7 (GND), U17.2 (NC), U17.6 (GND), U17.8 (GND), U17.11 (NC), U17.12 (NC), U18.3 (GND), U18.8 (GND), U18.9 (GND)
IMU_SCL: R41.1, R55.2, R60.2
IMU_SDA: R40.1, R54.2, R59.2
unnamed: C80.1, U17.5 (C1)
unnamed: R40.2, TP79.1, U13.14 (SDA)
unnamed: R41.2, TP78.1, U13.13 (SCL)
unnamed: R54.1, TP98.1, U17.1 (SCL/SPC)
unnamed: R55.1, TP99.1, U17.4 (SDA/SDI/SDO)
unnamed: R59.1, TP106.1, U18.2 (SCL)
unnamed: R60.1, TP107.1, U18.4 (SDA)
unnamed: TP84.1, U13.4 (INT1)
unnamed: TP85.1, U13.9 (INT2)
unnamed: TP100.1, U17.7 (DRDY)
unnamed: TP108.1, U18.5 (SA0)
unnamed: TP109.1, U18.7 (INT_DRDY)
VCC_1V8: C72.1, C73.1, C77.1, C79.1, C81.1, C88.1, C89.1, C90.1, C91.1, U13.5 (VDDIO), U13.8 (VDD), U13.12 (CS), U17.3 (~CS), U17.9 (Vdd), U17.10 (Vdd_IO), U18.1 (Vdd_IO), U18.6 (~CS), U18.10 (VDD)
