tengigabytes/MokyaLora/hardware/kicad/KeyBoard.kicad_sch

## KiCad design hardware/kicad/KeyBoard.kicad_sch (2026-04-07)

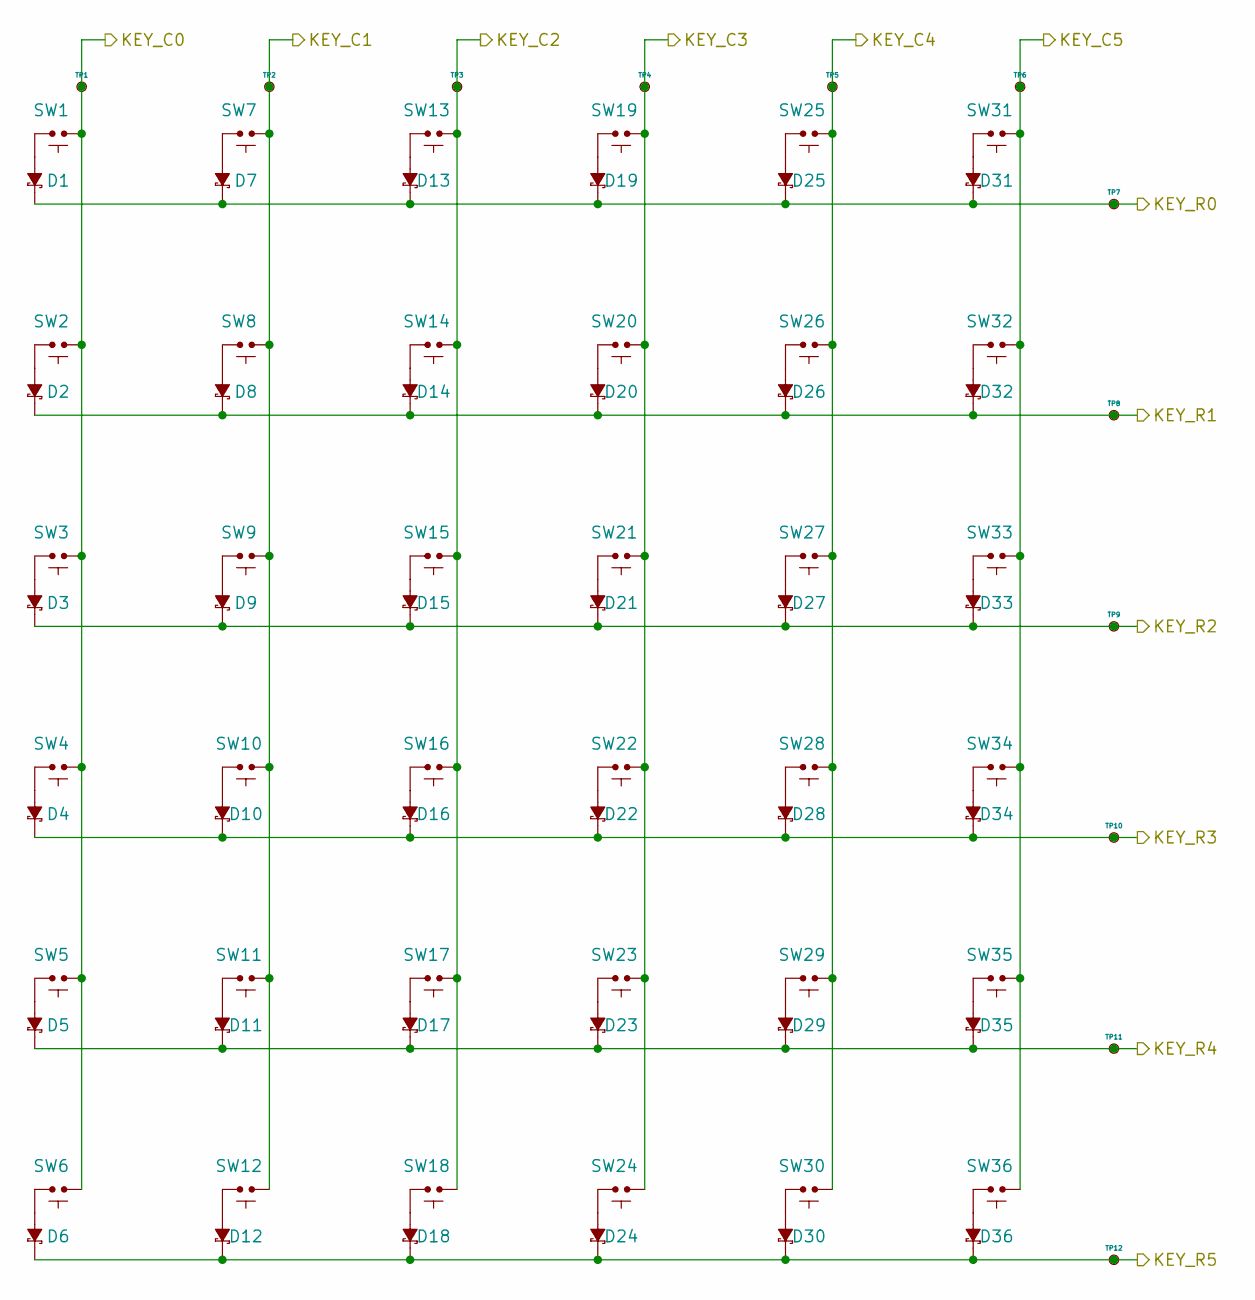
[picture p19: schematic KeyBoard.kicad_sch]

Parts:
D1, D2, D3, D4, D5, D6, D7, D8, D9, D10, D11, D12, D13, D14, D15, D16, D17, D18, D19, D20, D21, D22, D23, D24, D25, D26, D27, D28, D29, D30, D31, D32, D33, D34, D35, D36: D_SOD-523; MPN SDM03U40; LCSC C151333
SW1, SW2, SW3, SW4, SW5, SW6, SW7, SW8, SW9, SW10, SW11, SW12, SW13, SW14, SW15, SW16, SW17, SW18, SW19, SW20, SW21, SW22, SW23, SW24, SW25, SW26, SW27, SW28, SW29, SW30, SW31, SW32, SW33, SW34, SW35, SW36: SWT0105-003516JSA; SWT0105; MPN SWT0105-003516JSA
TP1, TP2, TP3, TP4, TP5, TP6, TP7, TP8, TP9, TP10, TP11, TP12: TestPoint_Small; TestPoint_Pad_D1.0mm; MPN test point

Connections:
KEY_C0: SW1.3, SW1.4, SW2.3, SW2.4, SW3.3, SW3.4, SW4.3, SW4.4, SW5.3, SW5.4, SW6.3, SW6.4, TP1.1
KEY_C1: SW7.3, SW7.4, SW8.3, SW8.4, SW9.3, SW9.4, SW10.3, SW10.4, SW11.3, SW11.4, SW12.3, SW12.4, TP2.1
KEY_C2: SW13.3, SW13.4, SW14.3, SW14.4, SW15.3, SW15.4, SW16.3, SW16.4, SW17.3, SW17.4, SW18.3, SW18.4, TP3.1
KEY_C3: SW19.3, SW19.4, SW20.3, SW20.4, SW21.3, SW21.4, SW22.3, SW22.4, SW23.3, SW23.4, SW24.3, SW24.4, TP4.1
KEY_C4: SW25.3, SW25.4, SW26.3, SW26.4, SW27.3, SW27.4, SW28.3, SW28.4, SW29.3, SW29.4, SW30.3, SW30.4, TP5.1
KEY_C5: SW31.3, SW31.4, SW32.3, SW32.4, SW33.3, SW33.4, SW34.3, SW34.4, SW35.3, SW35.4, SW36.3, SW36.4, TP6.1
KEY_R0: D1.C, D7.C, D13.C, D19.C, D25.C, D31.C, TP7.1
KEY_R1: D2.C, D8.C, D14.C, D20.C, D26.C, D32.C, TP8.1
KEY_R2: D3.C, D9.C, D15.C, D21.C, D27.C, D33.C, TP9.1
KEY_R3: D4.C, D10.C, D16.C, D22.C, D28.C, D34.C, TP10.1
KEY_R4: D5.C, D11.C, D17.C, D23.C, D29.C, D35.C, TP11.1
KEY_R5: D6.C, D12.C, D18.C, D24.C, D30.C, D36.C, TP12.1
unnamed: D1.A, SW1.1, SW1.2
unnamed: D2.A, SW2.1, SW2.2
unnamed: D3.A, SW3.1, SW3.2
unnamed: D4.A, SW4.1, SW4.2
unnamed: D5.A, SW5.1, SW5.2
unnamed: D6.A, SW6.1, SW6.2
unnamed: D7.A, SW7.1, SW7.2
unnamed: D8.A, SW8.1, SW8.2
unnamed: D9.A, SW9.1, SW9.2
unnamed: D10.A, SW10.1, SW10.2
unnamed: D11.A, SW11.1, SW11.2
unnamed: D12.A, SW12.1, SW12.2
unnamed: D13.A, SW13.1, SW13.2
unnamed: D14.A, SW14.1, SW14.2
unnamed: D15.A, SW15.1, SW15.2
unnamed: D16.A, SW16.1, SW16.2
unnamed: D17.A, SW17.1, SW17.2
unnamed: D18.A, SW18.1, SW18.2
unnamed: D19.A, SW19.1, SW19.2
unnamed: D20.A, SW20.1, SW20.2
unnamed: D21.A, SW21.1, SW21.2
unnamed: D22.A, SW22.1, SW22.2
unnamed: D23.A, SW23.1, SW23.2
unnamed: D24.A, SW24.1, SW24.2
unnamed: D25.A, SW25.1, SW25.2
unnamed: D26.A, SW26.1, SW26.2
unnamed: D27.A, SW27.1, SW27.2
unnamed: D28.A, SW28.1, SW28.2
unnamed: D29.A, SW29.1, SW29.2
unnamed: D30.A, SW30.1, SW30.2
unnamed: D31.A, SW31.1, SW31.2
unnamed: D32.A, SW32.1, SW32.2
unnamed: D33.A, SW33.1, SW33.2
unnamed: D34.A, SW34.1, SW34.2
unnamed: D35.A, SW35.1, SW35.2
unnamed: D36.A, SW36.1, SW36.2
