tengigabytes/MokyaLora/hardware/kicad/LCD.kicad_sch

## KiCad design hardware/kicad/LCD.kicad_sch (2026-03-22)

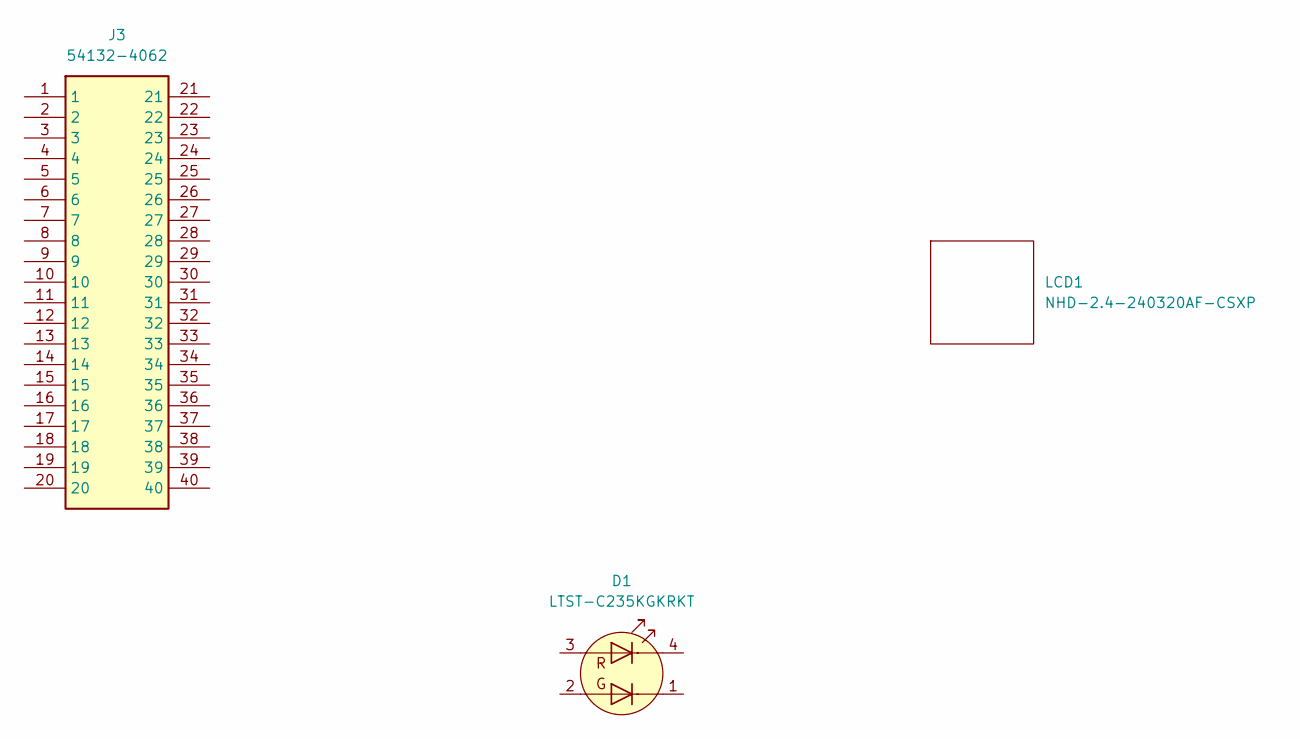
[picture p20: schematic LCD.kicad_sch]

Parts:
D1: LTST-C235KGKRKT; LED_LiteOn_LTST-C235KGKRKT
J3: 54132-4062; 54132-4062_1; Mouser Part Number 538-54132-4062
LCD1: NHD-2.4-240320AF-CSXP
