tengigabytes/MokyaLora/hardware/kicad/LORA.kicad_sch

## KiCad design hardware/kicad/LORA.kicad_sch (2026-04-07)

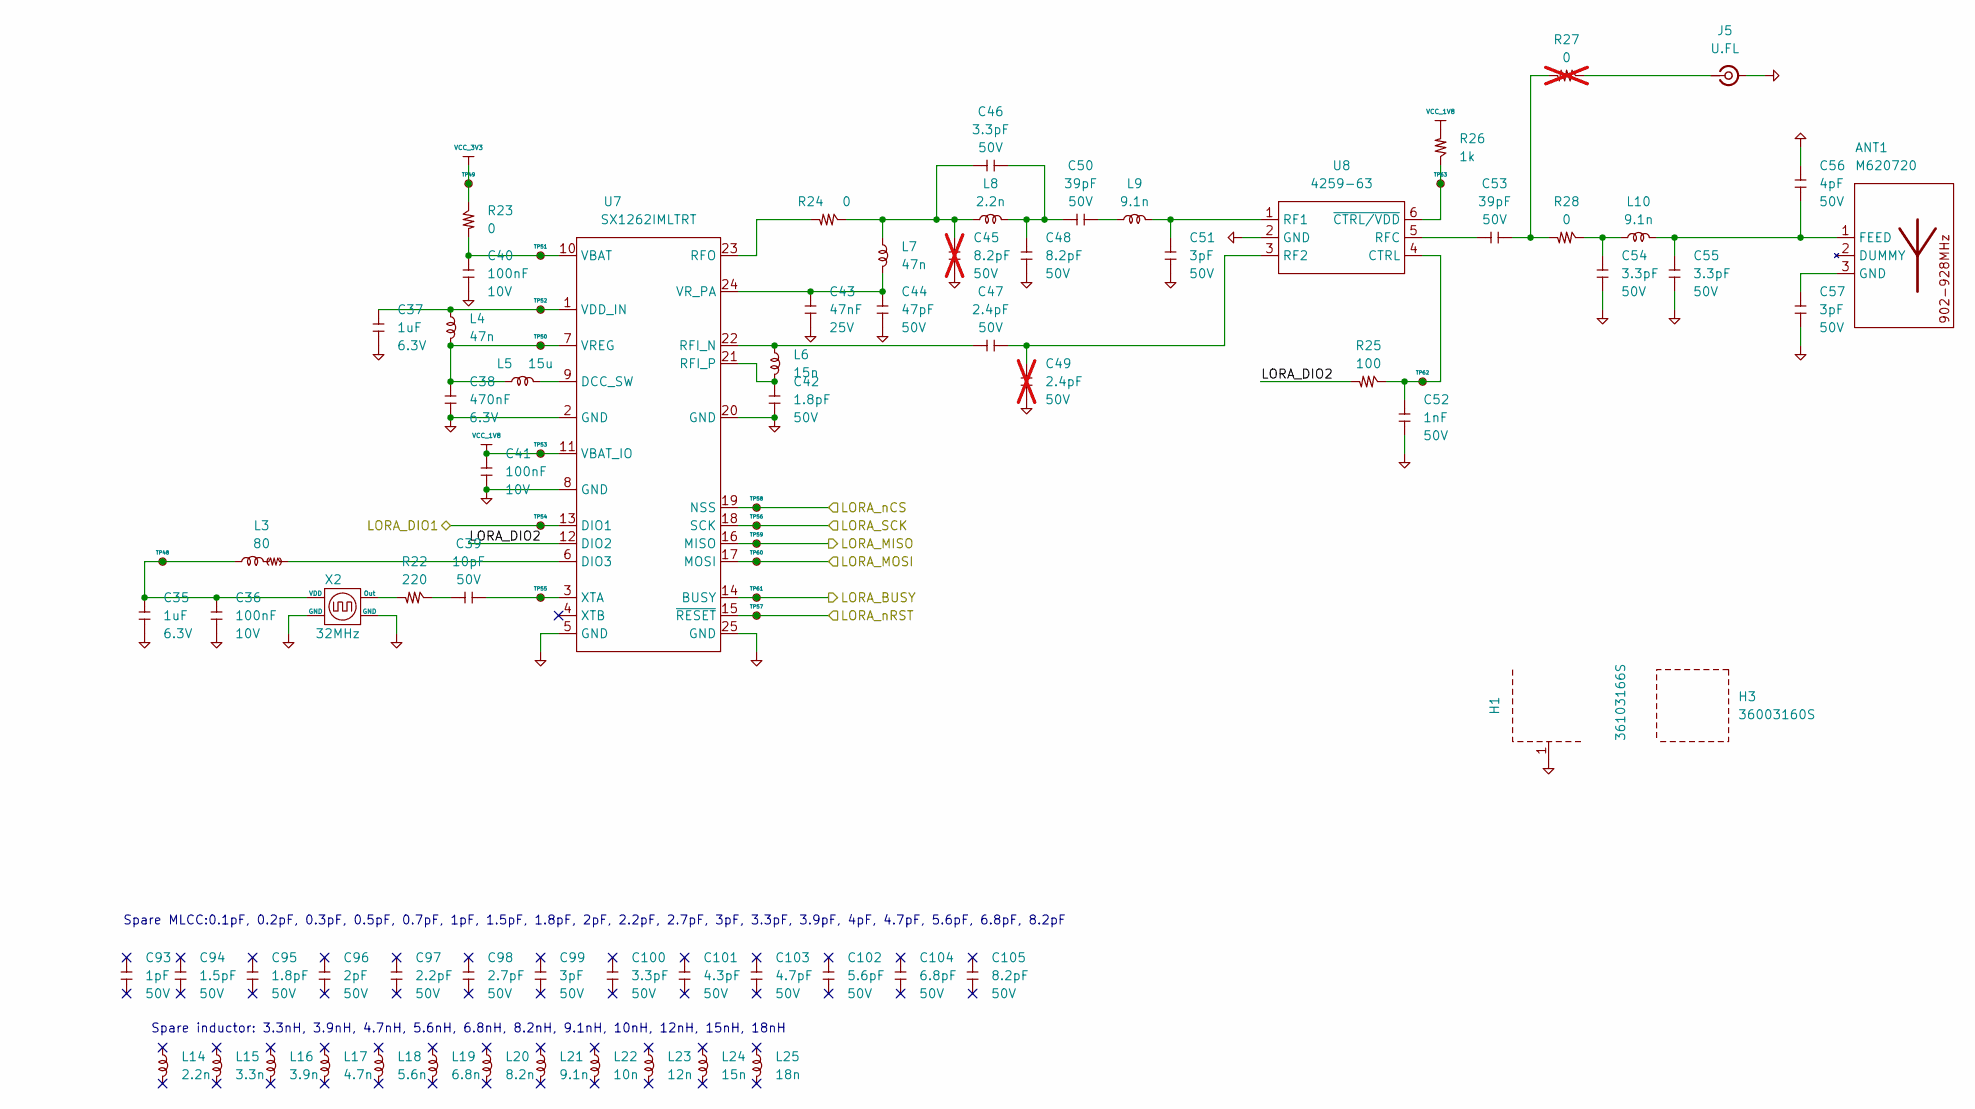
[picture p21: schematic LORA.kicad_sch]

Parts:
ANT1: M620720; Mouser Part Number 581-M620720
C35, C37: 1uF; C_0402_1005; Voltage 6.3V; MPN AC0402KRX5R5BB105; LCSC C3873469
C36, C40, C41: 100nF; C_0402_1005; Voltage 10V; MPN AC0402KRX7R6BB104; LCSC C3830899
C38: 470nF; C_0402_1005; Voltage 6.3V; MPN AC0402KRX5R5BB474; LCSC C3874572
C39: 10pF; C_0402_1005; Voltage 50V; MPN AC0402FRNPO9BN100; LCSC C3864989
C42: 1.8pF; C_0402_1005; Voltage 50V; MPN AC0402BRNPO9BN1R8; LCSC C2838743
C43: 47nF; C_0402_1005; Voltage 25V; MPN AC0402KRX7R8BB473; LCSC C726525
C44: 47pF; C_0402_1005; Voltage 50V; MPN AC0402JRNPO9BN470; LCSC C605203
C45: 8.2pF; C_0402_1005; Voltage 50V; MPN AC0402DRNPO9BN8R2; LCSC C1852948; not fitted
C46: 3.3pF; C_0402_1005; Voltage 50V; MPN AC0402BRNPO9BN3R3; LCSC C5182433
C47: 2.4pF; C_0402_1005; Voltage 50V; MPN AC0402BRNPO9BN2R4; LCSC C2180898
C48: 8.2pF; C_0402_1005; Voltage 50V; MPN AC0402DRNPO9BN8R2; LCSC C1852948
C49: 2.4pF; C_0402_1005; Voltage 50V; MPN AC0402BRNPO9BN2R4; LCSC C2180898; not fitted
C50: 39pF; C_0402_1005; Voltage 50V; MPN AC0402FRNPO9BN390; LCSC C1852942
C51, C57: 3pF; C_0402_1005; Voltage 50V; MPN AC0402CRNPO9BN3R0; LCSC C726109
C52: 1nF; C_0402_1005; Voltage 50V; MPN AC0402JRX7R9BB102; LCSC C726132
C53: 39pF; C_0402_1005; Voltage 50V; MPN AC0402GRNPO9BN390; LCSC C6458766
C54, C55: 3.3pF; C_0402_1005; Voltage 50V; MPN AC0402CRNPO9BN3R3; LCSC C326841
C56: 4pF; C_0402_1005; Voltage 50V; MPN AC0402CRNPO9BN4R0; LCSC C726111
C93: 1pF; C_0402_1005; Voltage 50V; MPN AC0402BRNPO9BN1R0
C94: 1.5pF; C_0402_1005; Voltage 50V; MPN AC0402BRNPO9BN1R5
C95: 1.8pF; C_0402_1005; Voltage 50V; MPN AC0402BRNPO9BN1R8
C96: 2pF; C_0402_1005; Voltage 50V; MPN AC0402BRNPO9BN2R0
C97: 2.2pF; C_0402_1005; Voltage 50V; MPN AC0402BRNPO9BN2R2
C98: 2.7pF; C_0402_1005; Voltage 50V; MPN AC0402BRNPO9BN2R7
C99: 3pF; C_0402_1005; Voltage 50V; MPN AC0402BRNPO9BN3R0
C100: 3.3pF; C_0402_1005; Voltage 50V; MPN AC0402BRNPO9BN3R3
C101: 4.3pF; C_0402_1005; Voltage 50V; MPN AC0402BRNPO9BN4R3
C102: 5.6pF; C_0402_1005; Voltage 50V; MPN AC0402BRNPO9BN5R6
C103: 4.7pF; C_0402_1005; Voltage 50V; MPN AC0402BRNPO9BN4R7
C104: 6.8pF; C_0402_1005; Voltage 50V; MPN AC0402BRNPO9BN6R8
C105: 8.2pF; C_0402_1005; Voltage 50V; MPN AC0402BRNPO9BN8R2
H1: 36103166S; Part Number 36103166S; LCSC C7464147
H3: 36003160S; MPN 36003160S
J5: U.FL; U.FL_Hirose_U.FL-R-SMT-1_Vertical; MPN U.FL-R-SMT-1; LCSC C88374
L3: 80; B_0402_1005; MPN BLM15PX800SN1D; LCSC C160978
L4, L7: 47n; L_0402_1005; MPN LQW15AN47NG80D; LCSC C237556
L5: 15u; L_0603_1608; MPN MLZ1608N150LT000; LCSC C1330243
L6: 15n; L_0402_1005; MPN LQW15AN15NG80D; LCSC C668460
L8: 2.2n; L_0402_1005; MPN LQW15AN2N2G80D; LCSC C412264
L9, L10: 9.1n; L_0402_1005; MPN LQW15AN9N1G80D; LCSC C113122
L14: 2.2n; L_0402_1005; MPN LQW15AN2N2G80D
L15: 3.3n; L_0402_1005; MPN LQW15AN3N3G80D
L16: 3.9n; L_0402_1005; MPN LQW15AN3N9G80D
L17: 4.7n; L_0402_1005; MPN LQW15AN4N7G80D
L18: 5.6n; L_0402_1005; MPN LQW15AN5N6G80D
L19: 6.8n; L_0402_1005; MPN LQW15AN6N8G80D
L20: 8.2n; L_0402_1005; MPN LQW15AN8N2G80D
L21: 9.1n; L_0402_1005; MPN LQW15AN9N1G80D
L22: 10n; L_0402_1005; MPN LQW15AN10NG80D
L23: 12n; L_0402_1005; MPN LQW15AN12NG80D
L24: 15n; L_0402_1005; MPN LQW15AN15NG80D
L25: 18n; L_0402_1005; MPN LQW15AN18NG80D
R22: 220; R_0402_1005; MPN AC0402FR-7W220RL; LCSC C6458714
R23, R24, R28: 0; R_0402_1005; MPN AC0402FR-070RL; LCSC C226739
R25: 100; R_0402_1005; MPN AC0402FR-7W100RL; LCSC C850722
R26: 1k; R_0402_1005; MPN AC0402FR-7W1KL; LCSC C5455561
R27: 0; R_0402_1005; MPN AC0402FR-070RL; LCSC C226739; not fitted
TP48, TP49, TP50, TP51, TP52, TP53, TP54, TP55, TP56, TP57, TP58, TP59, TP60, TP61, TP62, TP63: TestPoint_Small; TestPoint_Pad_D1.0mm; MPN test point
U7: SX1262IMLTRT; QFN-24-1EP_4x4mm_P0.5mm_EP2.6x2.6mm; MPN SX1262IMLTRT; LCSC C191341
U8: 4259-63; SOT65P210X110-6N; Mouser Part Number 81-4259-63
X2: 32MHz; Crystal_SMD_2016-4Pin_2.0x1.6mm; MPN ECS-TXO-20CSMV4-320-AY-TR; LCSC C19858587

Connections:
GND: C35.2, C36.2, C37.2, C38.2, C40.2, C41.2, C42.2, C43.2, C44.2, C45.2, C48.2, C49.2, C51.2, C52.2, C54.2, C55.2, C56.1, C57.2, H1.1, J5.2 (Ext), U7.2 (GND), U7.5 (GND), U7.8 (GND), U7.20 (GND), U7.25 (GND), U8.2 (GND), X2.1 (GND), X2.2 (GND)
LORA_BUSY: TP61.1, U7.14 (BUSY)
LORA_DIO1: TP54.1, U7.13 (DIO1)
LORA_DIO2: R25.1, U7.12 (DIO2)
LORA_MISO: TP59.1, U7.16 (MISO)
LORA_MOSI: TP60.1, U7.17 (MOSI)
LORA_SCK: TP56.1, U7.18 (SCK)
LORA_nCS: TP58.1, U7.19 (NSS)
LORA_nRST: TP57.1, U7.15 (~RESET)
unnamed: ANT1.1 (FEED), C55.1, C56.2, L10.2
unnamed: ANT1.3 (GND), C57.1
unnamed: C35.1, C36.1, L3.1, TP48.1, X2.4 (VDD)
unnamed: C37.1, L4.1, TP52.1, U7.1 (VDD_IN)
unnamed: C38.1, L4.2, L5.1, TP50.1, U7.7 (VREG)
unnamed: C39.1, R22.2
unnamed: C39.2, TP55.1, U7.3 (XTA)
unnamed: C40.1, R23.1, TP51.1, U7.10 (VBAT)
unnamed: C42.1, L6.2, U7.21 (RFI_P)
unnamed: C43.1, C44.1, L7.2, U7.24 (VR_PA)
unnamed: C45.1, C46.1, L7.1, L8.1, R24.2
unnamed: C46.2, C48.1, C50.1, L8.2
unnamed: C47.1, L6.1, U7.22 (RFI_N)
unnamed: C47.2, C49.1, U8.3 (RF2)
unnamed: C50.2, L9.1
unnamed: C51.1, L9.2, U8.1 (RF1)
unnamed: C52.1, R25.2, TP62.1, U8.4 (CTRL)
unnamed: C53.1, U8.5 (RFC)
unnamed: C53.2, R27.1, R28.1
unnamed: C54.1, L10.1, R28.2
unnamed: J5.1 (In), R27.2
unnamed: L3.2, U7.6 (DIO3)
unnamed: L5.2, U7.9 (DCC_SW)
unnamed: R22.1, X2.3 (Out)
unnamed: R24.1, U7.23 (RFO)
unnamed: R26.2, TP63.1, U8.6 (~CTRL/VDD)
VCC_1V8: C41.1, R26.1, TP53.1, U7.11 (VBAT_IO)
VCC_3V3: R23.2, TP49.1

Notes on the sheet:
Spare MLCC:0.1pF, 0.2pF, 0.3pF, 0.5pF, 0.7pF, 1pF, 1.5pF, 1.8pF, 2pF, 2.2pF, 2.7pF, 3pF, 3.3pF, 3.9pF, 4pF, 4.7pF, 5.6pF, 6.8pF, 8.2pF
Spare inductor: 3.3nH, 3.9nH, 4.7nH, 5.6nH, 6.8nH, 8.2nH, 9.1nH, 10nH, 12nH, 15nH, 18nH
