tengigabytes/MokyaLora/hardware/kicad/MCU_M5531.kicad_sch

## KiCad design hardware/kicad/MCU_M5531.kicad_sch (2026-03-22)

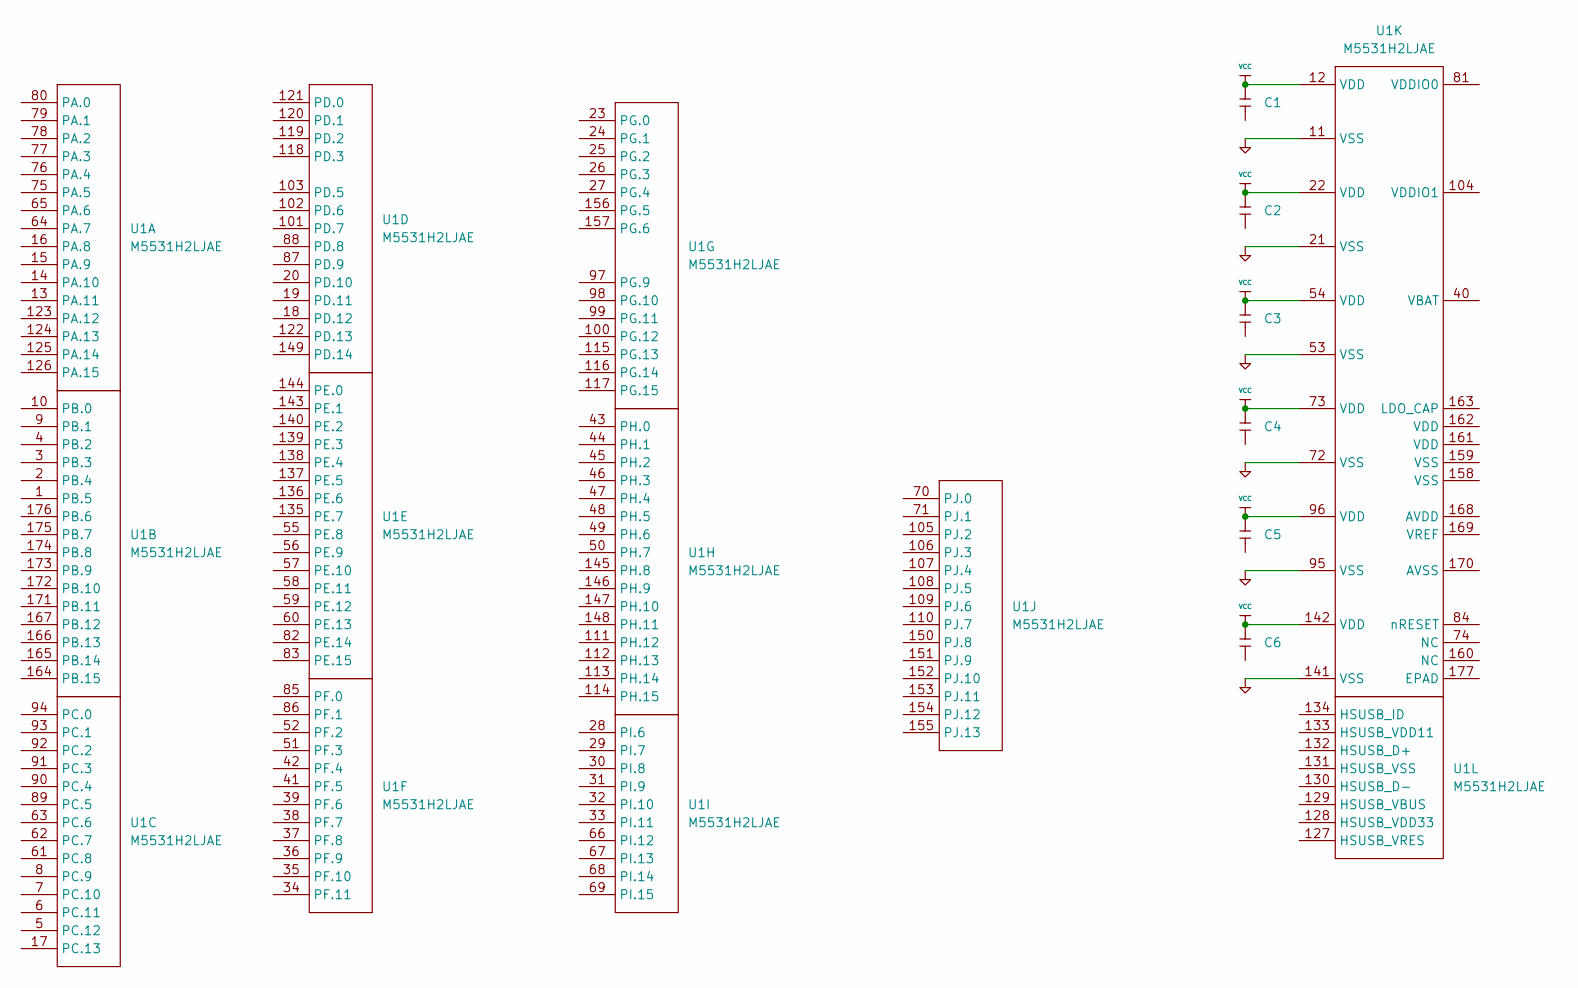
[picture p22: schematic MCU_M5531.kicad_sch]

Parts:
C1, C2, C3, C4, C5, C6: (no value)
U1: M5531H2LJAE; LQFP-176-1EP_24x24mm_P0.5mm_EP6.6x6.6mm

Connections:
GND: U1.11 (VSS), U1.21 (VSS), U1.53 (VSS), U1.72 (VSS), U1.95 (VSS), U1.141 (VSS)
VCC: C1.1, C2.1, C3.1, C4.1, C5.1, C6.1, U1.12 (VDD), U1.22 (VDD), U1.54 (VDD), U1.73 (VDD), U1.96 (VDD), U1.142 (VDD)
