tengigabytes/MokyaLora/hardware/kicad/MCU_RP2350B.kicad_sch

## KiCad design hardware/kicad/MCU_RP2350B.kicad_sch (2026-04-07)

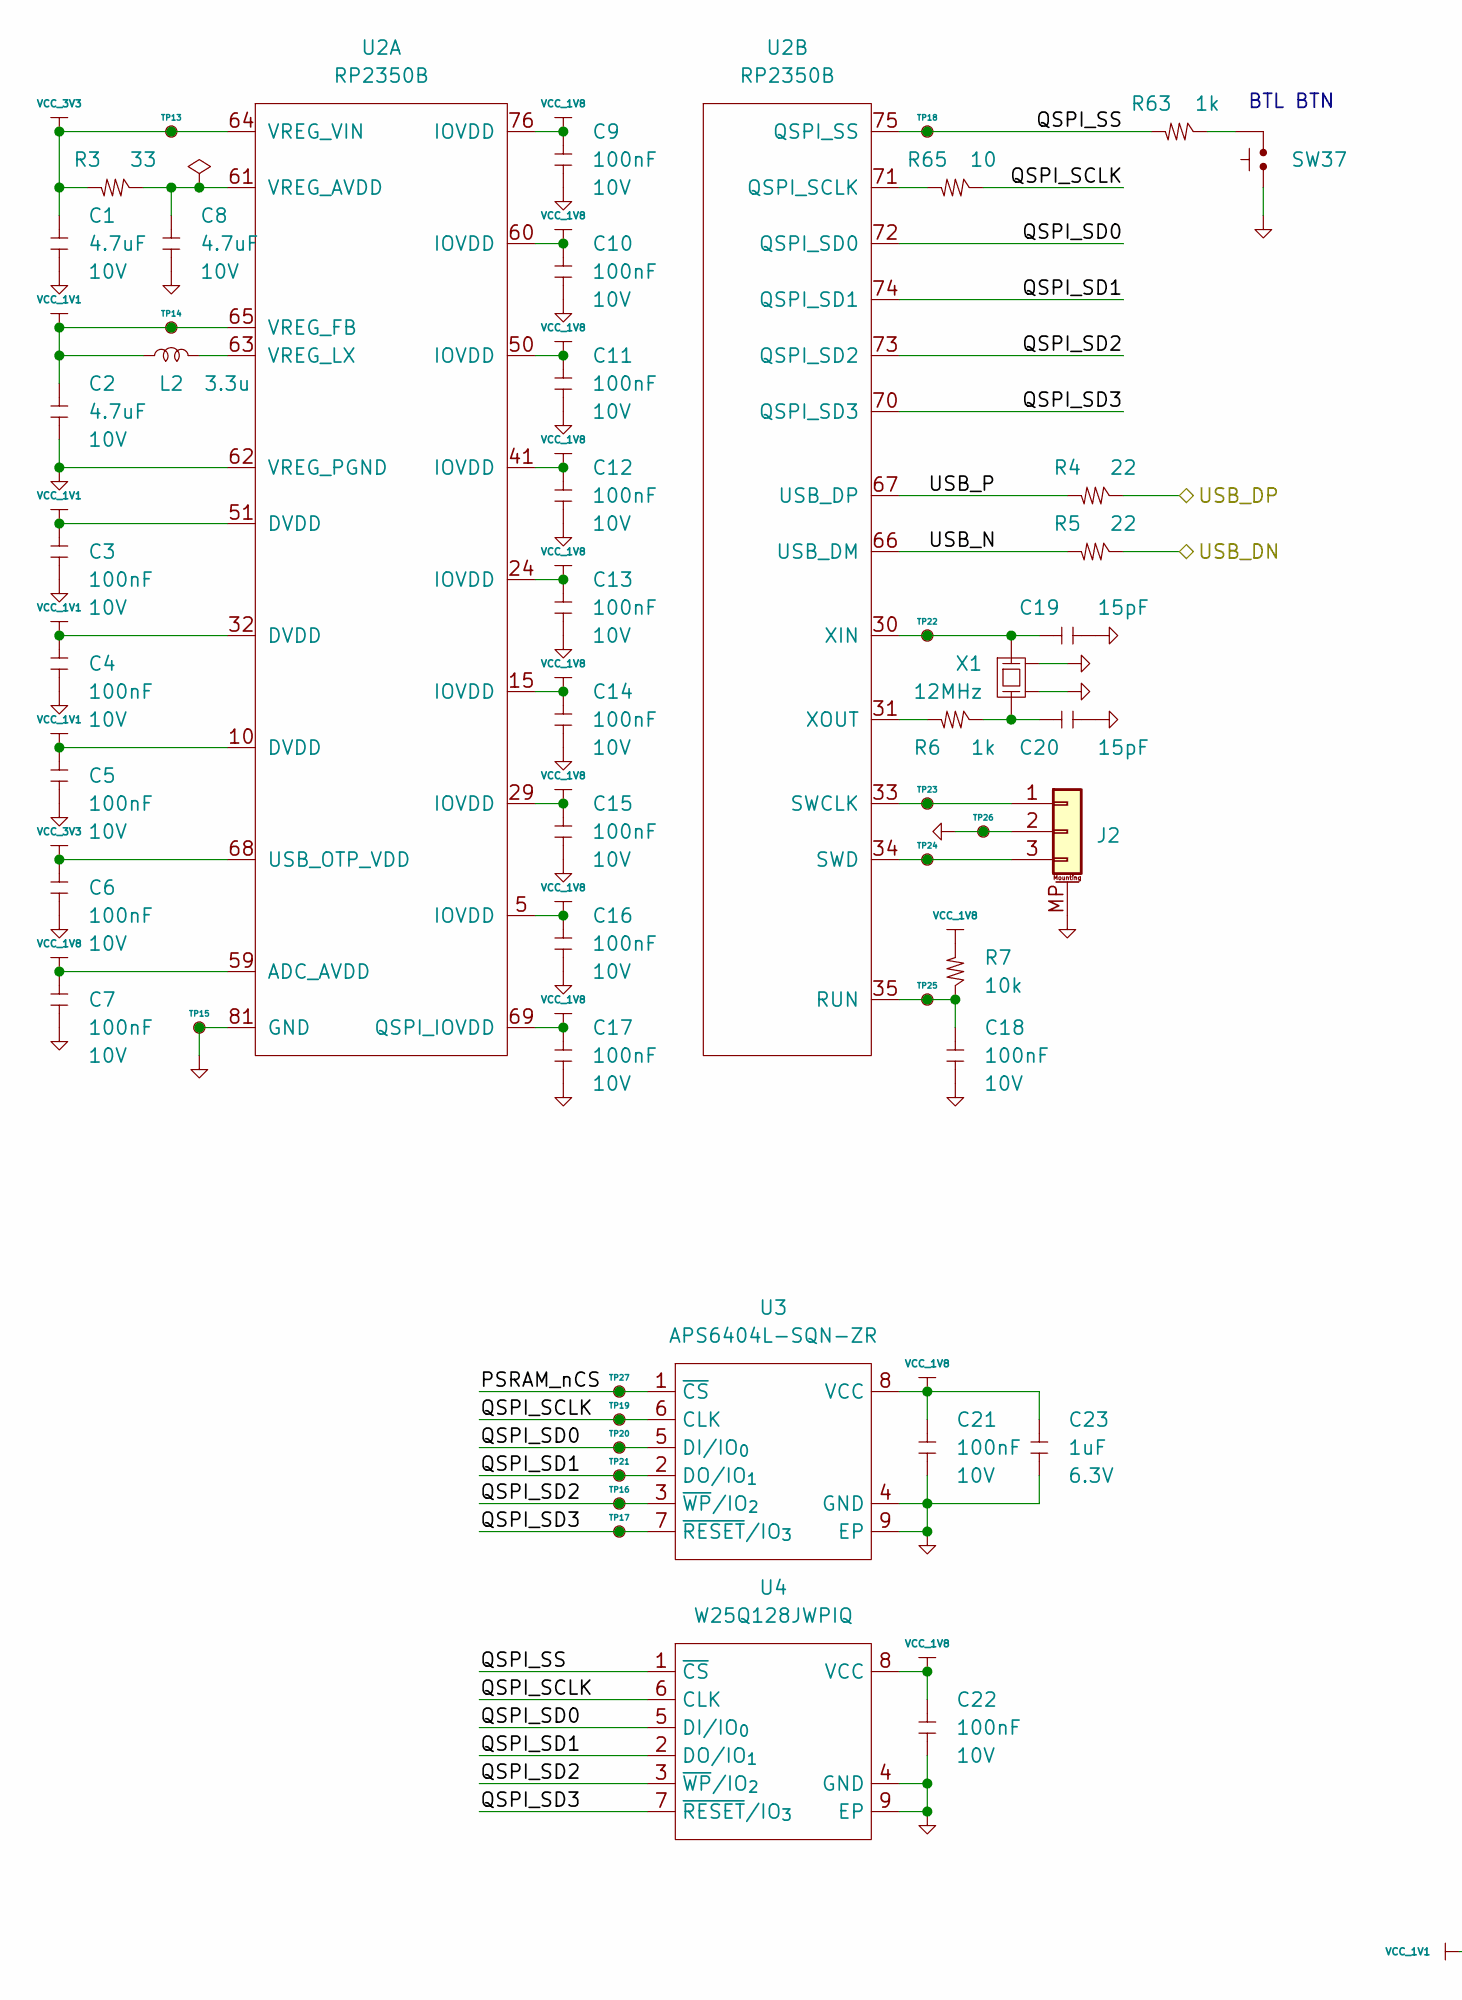
[picture p23: schematic MCU_RP2350B.kicad_sch, part in row 1, column 1]

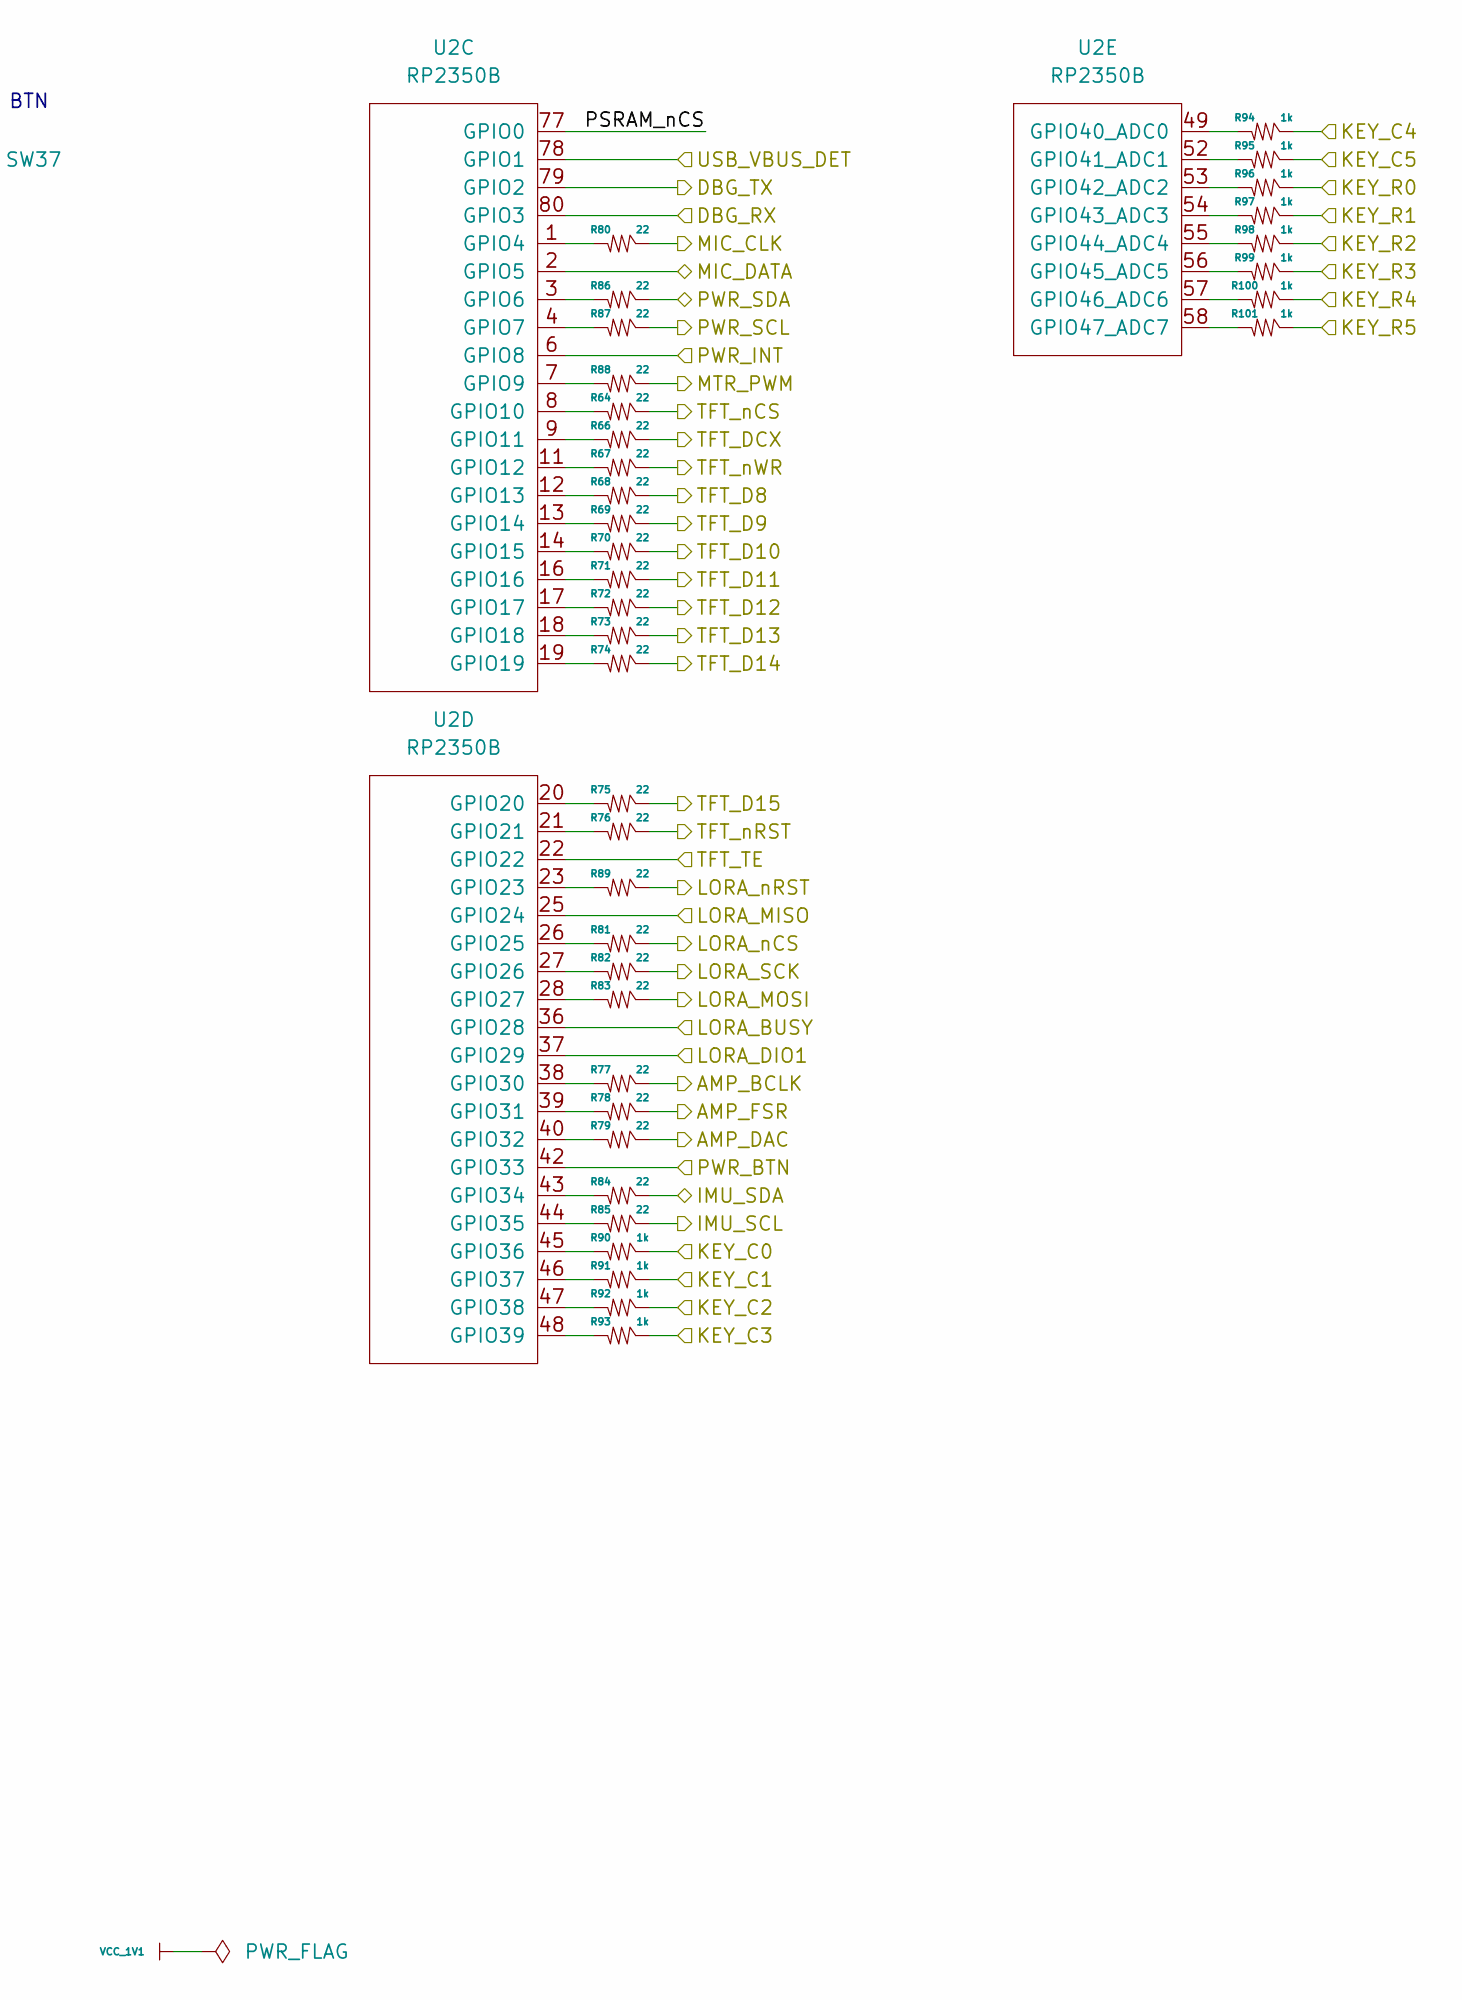
[picture p24: schematic MCU_RP2350B.kicad_sch, part in row 1, column 2]

Parts:
C1, C2, C8: 4.7uF; C_0402_1005; Voltage 10V; MPN CC0402KRX5R6BB475; LCSC C326586
C3, C4, C5, C6, C7, C9, C10, C11, C12, C13, C14, C15, C16, C17, C18, C21, C22: 100nF; C_0402_1005; Voltage 10V; MPN AC0402KRX7R6BB104; LCSC C3830899
C19, C20: 15pF; C_0402_1005; Voltage 50V; MPN AC0402FRNPO9BN150; LCSC C2191719
C23: 1uF; C_0402_1005; Voltage 6.3V; MPN AC0402KRX5R5BB105; LCSC C3873469
J2: SM03B-SRSS-TB; JST_SH_SM03B-SRSS-TB_1x03-1MP_P1.00mm_Horizontal; MPN SM03B-SRSS-TB; LCSC C160403
L2: 3.3u; L_0806_2016; MPN AOTA-B201610S3R3-101-T; LCSC C42411119
R3: 33; R_0402_1005; MPN AC0402FR-7W33RL; LCSC C5552170
R4, R5, R64, R66, R67, R68, R69, R70, R71, R72, R73, R74, R75, R76, R77, R78, R79, R80, R81, R82, R83, R84, R85, R86, R87, R88, R89: 22; R_0402_1005; MPN AC0402FR-7W22RL; LCSC C6117666
R6, R63, R90, R91, R92, R93, R94, R95, R96, R97, R98, R99, R100, R101: 1k; R_0402_1005; MPN AC0402FR-7W1KL; LCSC C5455561
R7: 10k; R_0402_1005; MPN AC0402FR-7W10KL; LCSC C850723
R65: 10; R_0402_1005; MPN AC0402FR-7W10RL; LCSC C5455560
SW37: SWT0105-003516JSA; SWT0105; MPN SWT0105-003516JSA
TP13, TP14, TP15, TP16, TP17, TP18, TP19, TP20, TP21, TP22, TP23, TP24, TP25, TP26, TP27: TestPoint_Small; TestPoint_Pad_D1.0mm; MPN test point
U2: RP2350B; RP2350-QFN-80-1EP_10x10_P0.4mm_EP3.4x3.4mm_ThermalVias; MPN SC1510-A4; LCSC C42415655
U3: APS6404L-SQN-ZR; Winbond_USON-8-1EP_3x2mm_P0.5mm_EP0.2x1.6mm; MPN APS6404L-SQN-ZR; LCSC C5360305
U4: W25Q128JWPIQ; WSON-8-1EP_6x5mm_P1.27mm_EP3.4x4.3mm; MPN W25Q128JWPIQ; LCSC C2689660
X1: 12MHz; Crystal_SMD_3225-4Pin_3.2x2.5mm; MPN ABM8-272-T3; LCSC C20625731

Connections:
AMP_BCLK: R77.2
AMP_DAC: R79.2
AMP_FSR: R78.2
DBG_RX: U2.80 (GPIO3)
DBG_TX: U2.79 (GPIO2)
GND: C1.2, C2.2, C3.2, C4.2, C5.2, C6.2, C7.2, C8.2, C9.2, C10.2, C11.2, C12.2, C13.2, C14.2, C15.2, C16.2, C17.2, C18.2, C19.2, C20.2, C21.2, C22.2, C23.2, J2.2, J2.MP (MountPin), SW37.3, SW37.4, TP15.1, TP26.1, U2.62 (VREG_PGND), U2.81 (GND), U3.4 (GND), U3.9 (EP), U4.4 (GND), U4.9 (EP), X1.2, X1.4
IMU_SCL: R85.2
IMU_SDA: R84.2
KEY_C0: R90.2
KEY_C1: R91.2
KEY_C2: R92.2
KEY_C3: R93.2
KEY_C4: R94.2
KEY_C5: R95.2
KEY_R0: R96.2
KEY_R1: R97.2
KEY_R2: R98.2
KEY_R3: R99.2
KEY_R4: R100.2
KEY_R5: R101.2
LORA_BUSY: U2.36 (GPIO28)
LORA_DIO1: U2.37 (GPIO29)
LORA_MISO: U2.25 (GPIO24)
LORA_MOSI: R83.2
LORA_SCK: R82.2
LORA_nCS: R81.2
LORA_nRST: R89.2
MIC_CLK: R80.2
MIC_DATA: U2.2 (GPIO5)
MTR_PWM: R88.2
unnamed: C8.1, R3.2, U2.61 (VREG_AVDD)
unnamed: C18.1, R7.2, TP25.1, U2.35 (RUN)
unnamed: C19.1, TP22.1, U2.30 (XIN), X1.1
unnamed: C20.1, R6.2, X1.3
unnamed: J2.1, TP23.1, U2.33 (SWCLK)
unnamed: J2.3, TP24.1, U2.34 (SWD)
unnamed: L2.2, U2.63 (VREG_LX)
unnamed: R6.1, U2.31 (XOUT)
unnamed: R63.2, SW37.1, SW37.2
unnamed: R64.1, U2.8 (GPIO10)
unnamed: R65.1, U2.71 (QSPI_SCLK)
unnamed: R66.1, U2.9 (GPIO11)
unnamed: R67.1, U2.11 (GPIO12)
unnamed: R68.1, U2.12 (GPIO13)
unnamed: R69.1, U2.13 (GPIO14)
unnamed: R70.1, U2.14 (GPIO15)
unnamed: R71.1, U2.16 (GPIO16)
unnamed: R72.1, U2.17 (GPIO17)
unnamed: R73.1, U2.18 (GPIO18)
unnamed: R74.1, U2.19 (GPIO19)
unnamed: R75.1, U2.20 (GPIO20)
unnamed: R76.1, U2.21 (GPIO21)
unnamed: R77.1, U2.38 (GPIO30)
unnamed: R78.1, U2.39 (GPIO31)
unnamed: R79.1, U2.40 (GPIO32)
unnamed: R80.1, U2.1 (GPIO4)
unnamed: R81.1, U2.26 (GPIO25)
unnamed: R82.1, U2.27 (GPIO26)
unnamed: R83.1, U2.28 (GPIO27)
unnamed: R84.1, U2.43 (GPIO34)
unnamed: R85.1, U2.44 (GPIO35)
unnamed: R86.1, U2.3 (GPIO6)
unnamed: R87.1, U2.4 (GPIO7)
unnamed: R88.1, U2.7 (GPIO9)
unnamed: R89.1, U2.23 (GPIO23)
unnamed: R90.1, U2.45 (GPIO36)
unnamed: R91.1, U2.46 (GPIO37)
unnamed: R92.1, U2.47 (GPIO38)
unnamed: R93.1, U2.48 (GPIO39)
unnamed: R94.1, U2.49 (GPIO40_ADC0)
unnamed: R95.1, U2.52 (GPIO41_ADC1)
unnamed: R96.1, U2.53 (GPIO42_ADC2)
unnamed: R97.1, U2.54 (GPIO43_ADC3)
unnamed: R98.1, U2.55 (GPIO44_ADC4)
unnamed: R99.1, U2.56 (GPIO45_ADC5)
unnamed: R100.1, U2.57 (GPIO46_ADC6)
unnamed: R101.1, U2.58 (GPIO47_ADC7)
PSRAM_nCS: TP27.1, U2.77 (GPIO0), U3.1 (~CS)
PWR_BTN: U2.42 (GPIO33)
PWR_INT: U2.6 (GPIO8)
PWR_SCL: R87.2
PWR_SDA: R86.2
QSPI_SCLK: R65.2, TP19.1, U3.6 (CLK), U4.6 (CLK)
QSPI_SD0: TP20.1, U2.72 (QSPI_SD0), U3.5 (DI/IO_{0}), U4.5 (DI/IO_{0})
QSPI_SD1: TP21.1, U2.74 (QSPI_SD1), U3.2 (DO/IO_{1}), U4.2 (DO/IO_{1})
QSPI_SD2: TP16.1, U2.73 (QSPI_SD2), U3.3 (~WP/IO_{2}), U4.3 (~WP/IO_{2})
QSPI_SD3: TP17.1, U2.70 (QSPI_SD3), U3.7 (~RESET/IO_{3}), U4.7 (~RESET/IO_{3})
QSPI_SS: R63.1, TP18.1, U2.75 (QSPI_SS), U4.1 (~CS)
TFT_D8: R68.2
TFT_D9: R69.2
TFT_D10: R70.2
TFT_D11: R71.2
TFT_D12: R72.2
TFT_D13: R73.2
TFT_D14: R74.2
TFT_D15: R75.2
TFT_DCX: R66.2
TFT_TE: U2.22 (GPIO22)
TFT_nCS: R64.2
TFT_nRST: R76.2
TFT_nWR: R67.2
USB_DN: R5.2
USB_DP: R4.2
USB_N: R5.1, U2.66 (USB_DM)
USB_P: R4.1, U2.67 (USB_DP)
USB_VBUS_DET: U2.78 (GPIO1)
VCC_1V1: C2.1, C3.1, C4.1, C5.1, L2.1, TP14.1, U2.10 (DVDD), U2.32 (DVDD), U2.51 (DVDD), U2.65 (VREG_FB)
VCC_1V8: C7.1, C9.1, C10.1, C11.1, C12.1, C13.1, C14.1, C15.1, C16.1, C17.1, C21.1, C22.1, C23.1, R7.1, U2.5 (IOVDD), U2.15 (IOVDD), U2.24 (IOVDD), U2.29 (IOVDD), U2.41 (IOVDD), U2.50 (IOVDD), U2.59 (ADC_AVDD), U2.60 (IOVDD), U2.69 (QSPI_IOVDD), U2.76 (IOVDD), U3.8 (VCC), U4.8 (VCC)
VCC_3V3: C1.1, C6.1, R3.1, TP13.1, U2.64 (VREG_VIN), U2.68 (USB_OTP_VDD)

Notes on the sheet:
BTL BTN
