tengigabytes/MokyaLora/hardware/kicad/Microphone.kicad_sch

## KiCad design hardware/kicad/Microphone.kicad_sch (2026-04-07)

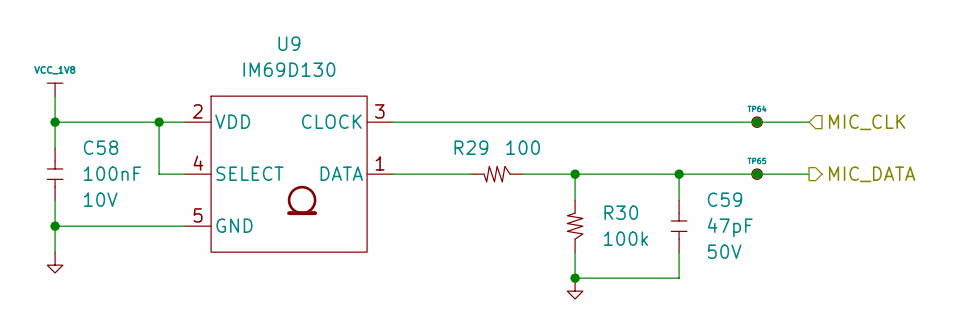
[picture p25: schematic Microphone.kicad_sch]

Parts:
C58: 100nF; C_0402_1005; Voltage 10V; MPN AC0402KRX7R6BB104; LCSC C3830899
C59: 47pF; C_0402_1005; Voltage 50V; MPN AC0402JRNPO9BN470; LCSC C605203
R29: 100; R_0402_1005; MPN AC0402FR-7W100RL; LCSC C850722
R30: 100k; R_0402_1005; MPN AC0402FR-07100KL; LCSC C144809
TP64, TP65: TestPoint_Small; TestPoint_Pad_D1.0mm; MPN test point
U9: IM69D130; Infineon_PG-LLGA-5-1; MPN IM69D130; LCSC C536262

Connections:
GND: C58.2, C59.2, R30.2, U9.5 (GND)
MIC_CLK: TP64.1, U9.3 (CLOCK)
MIC_DATA: C59.1, R29.2, R30.1, TP65.1
unnamed: R29.1, U9.1 (DATA)
VCC_1V8: C58.1, U9.2 (VDD), U9.4 (SELECT)
