tengigabytes/MokyaLora/hardware/kicad/MokyaLora.kicad_sch

## KiCad design hardware/kicad/MokyaLora.kicad_sch (2026-04-07)

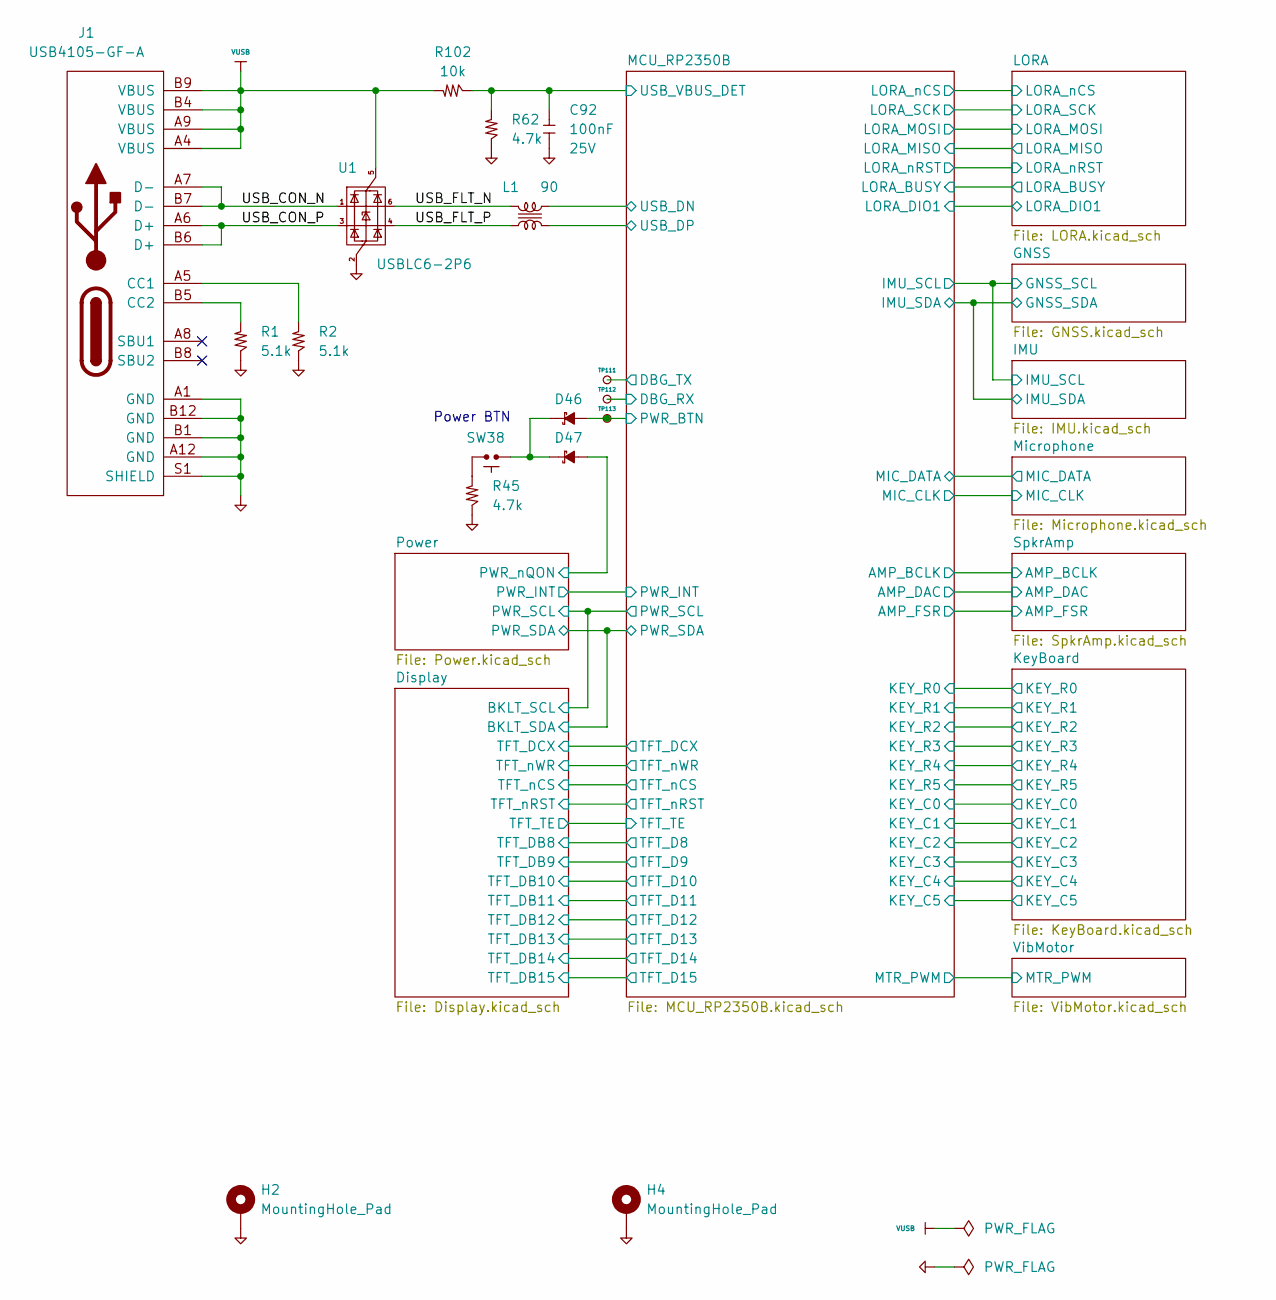
[picture p26: schematic MokyaLora.kicad_sch]

Parts:
C92: 100nF; C_0402_1005; Voltage 25V; MPN AC0402KRX7R8BB104; LCSC C726522
D46, D47: D_SOD-523; MPN SDM03U40; LCSC C151333
H2, H4: MountingHole_Pad; MountingHole_2.7mm_M2.5_Pad_Via; MPN MountingHole_Pad
J1: USB4105-GF-A; USB_C_Receptacle_GCT_USB4105-xx-A_16P_TopMnt_Horizontal; MPN USB4105-GF-A; LCSC C3020560
L1: 90; FIL_DLM0NSN900HY2D; MPN DLM0NSN900HY2D; LCSC C882594
R1, R2: 5.1k; R_0402_1005; MPN AC0402FR-7W5K1L; LCSC C20141810
R45, R62: 4.7k; R_0402_1005; MPN AC0402FR-7W4K7L; LCSC C5455562
R102: 10k; R_0402_1005; MPN AC0402FR-7W10KL; LCSC C850723
SW38: SWT0105-003516JSA; SWT0105; MPN SWT0105-003516JSA
TP111, TP112, TP113: TestPoint_Small; TestPoint_Pad_D1.0mm; MPN test point
U1: USBLC6-2P6; SOT-666; MPN USBLC6-2P6; LCSC C15999

Connections:
DBG_RX: TP112.1
DBG_TX: TP111.1
GND: C92.2, H2.1, H4.1, J1.A1 (GND), J1.A12 (GND), J1.B1 (GND), J1.B12 (GND), J1.S1 (SHIELD), R1.2, R2.2, R45.2, R62.2, U1.2 (GND)
unnamed: D46.C, D47.C, SW38.3, SW38.4
unnamed: J1.A5 (CC1), R2.1
unnamed: J1.B5 (CC2), R1.1
unnamed: R45.1, SW38.1, SW38.2
PWR_BTN: D46.A, TP113.1
PWR_nQON: D47.A
USB_CON_N: J1.A7 (D-), J1.B7 (D-), U1.1 (I/O1)
USB_CON_P: J1.A6 (D+), J1.B6 (D+), U1.3 (I/O2)
USB_DN: L1.2
USB_DP: L1.3
USB_FLT_N: L1.1, U1.6 (I/O1)
USB_FLT_P: L1.4, U1.4 (I/O2)
USB_VBUS_DET: C92.1, R62.1, R102.2
VUSB: J1.A4 (VBUS), J1.A9 (VBUS), J1.B4 (VBUS), J1.B9 (VBUS), R102.1, U1.5 (VBUS)

Notes on the sheet:
Power BTN
