tengigabytes/MokyaLora/hardware/kicad/PMIC.kicad_sch

## KiCad design hardware/kicad/PMIC.kicad_sch (2026-03-22)

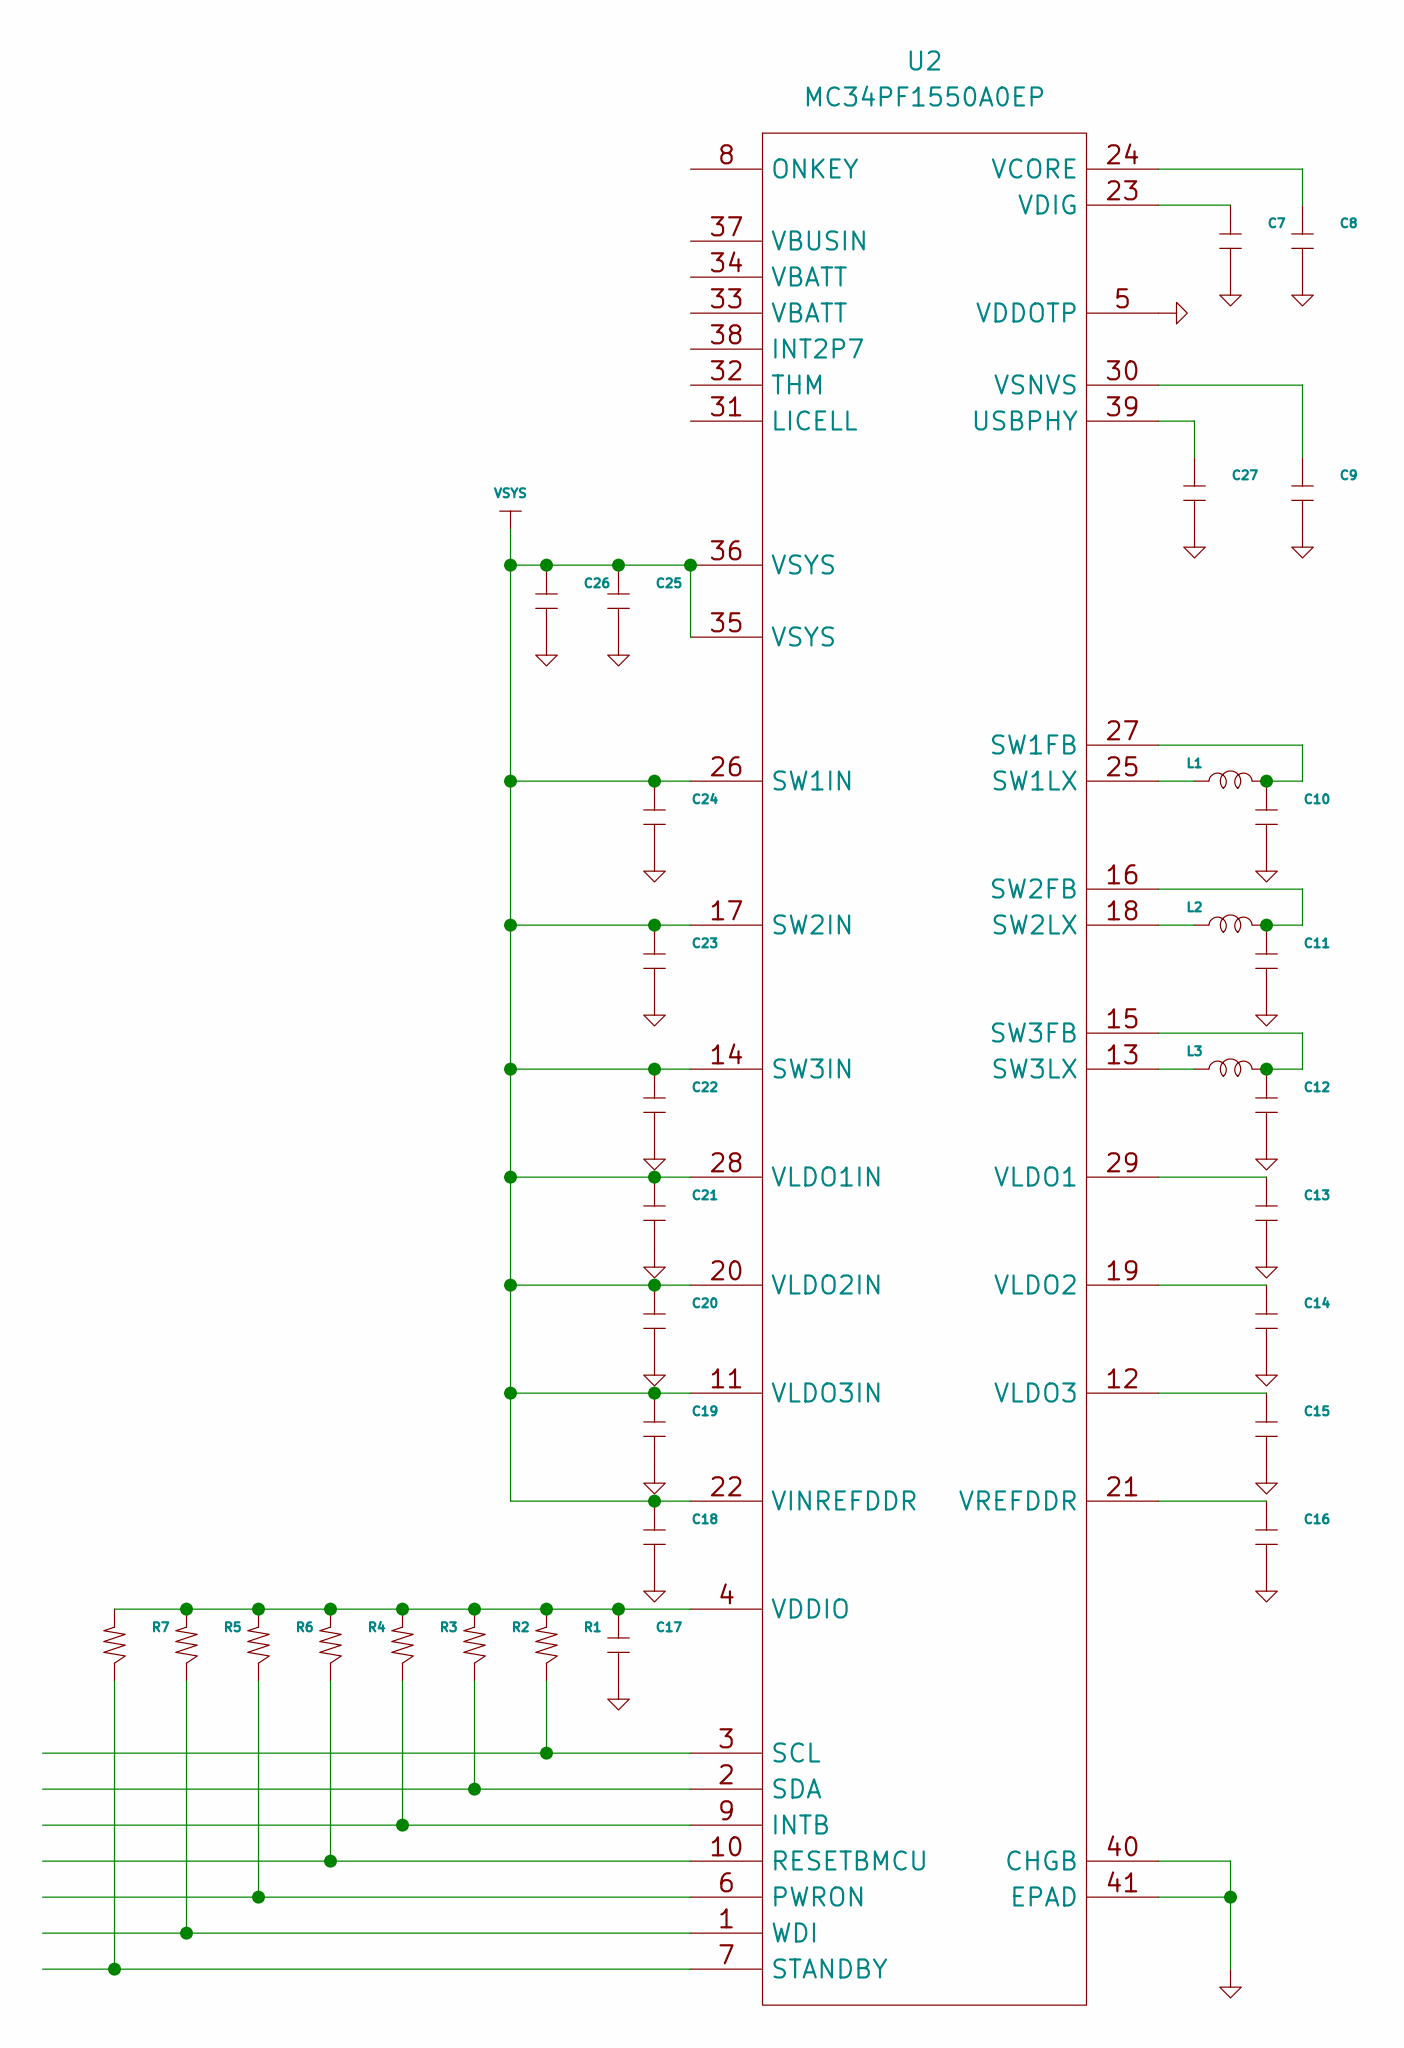
[picture p27: schematic PMIC.kicad_sch]

Parts:
C7, C8, C9, C10, C11, C12, C13, C14, C15, C16, C17, C18, C19, C20, C21, C22, C23, C24, C25, C26, C27: (no value)
L1, L2, L3: (no value)
R1, R2, R3, R4, R5, R6, R7: (no value)
U2: MC34PF1550A0EP; QFN-40-1EP_5x5mm_P0.4mm_EP3.8x3.8mm_ThermalVias

Connections:
GND: C7.2, C8.2, C9.2, C10.2, C11.2, C12.2, C13.2, C14.2, C15.2, C16.2, C17.2, C18.2, C19.2, C20.2, C21.2, C22.2, C23.2, C24.2, C25.2, C26.2, C27.2, U2.5 (VDDOTP), U2.40 (CHGB), U2.41 (EPAD)
unnamed: C7.1, U2.23 (VDIG)
unnamed: C8.1, U2.24 (VCORE)
unnamed: C9.1, U2.30 (VSNVS)
unnamed: C10.1, L1.2, U2.27 (SW1FB)
unnamed: C11.1, L2.2, U2.16 (SW2FB)
unnamed: C12.1, L3.2, U2.15 (SW3FB)
unnamed: C13.1, U2.29 (VLDO1)
unnamed: C14.1, U2.19 (VLDO2)
unnamed: C15.1, U2.12 (VLDO3)
unnamed: C16.1, U2.21 (VREFDDR)
unnamed: C17.1, R1.1, R2.1, R3.1, R4.1, R5.1, R6.1, R7.1, U2.4 (VDDIO)
unnamed: C27.1, U2.39 (USBPHY)
unnamed: L1.1, U2.25 (SW1LX)
unnamed: L2.1, U2.18 (SW2LX)
unnamed: L3.1, U2.13 (SW3LX)
unnamed: R1.2, U2.3 (SCL)
unnamed: R2.2, U2.2 (SDA)
unnamed: R3.2, U2.9 (INTB)
unnamed: R4.2, U2.10 (RESETBMCU)
unnamed: R5.2, U2.1 (WDI)
unnamed: R6.2, U2.6 (PWRON)
unnamed: R7.2, U2.7 (STANDBY)
VSYS: C18.1, C19.1, C20.1, C21.1, C22.1, C23.1, C24.1, C25.1, C26.1, U2.11 (VLDO3IN), U2.14 (SW3IN), U2.17 (SW2IN), U2.20 (VLDO2IN), U2.22 (VINREFDDR), U2.26 (SW1IN), U2.28 (VLDO1IN), U2.35 (VSYS), U2.36 (VSYS)
