tengigabytes/MokyaLora/hardware/kicad/Power.kicad_sch

## KiCad design hardware/kicad/Power.kicad_sch (2026-04-07)

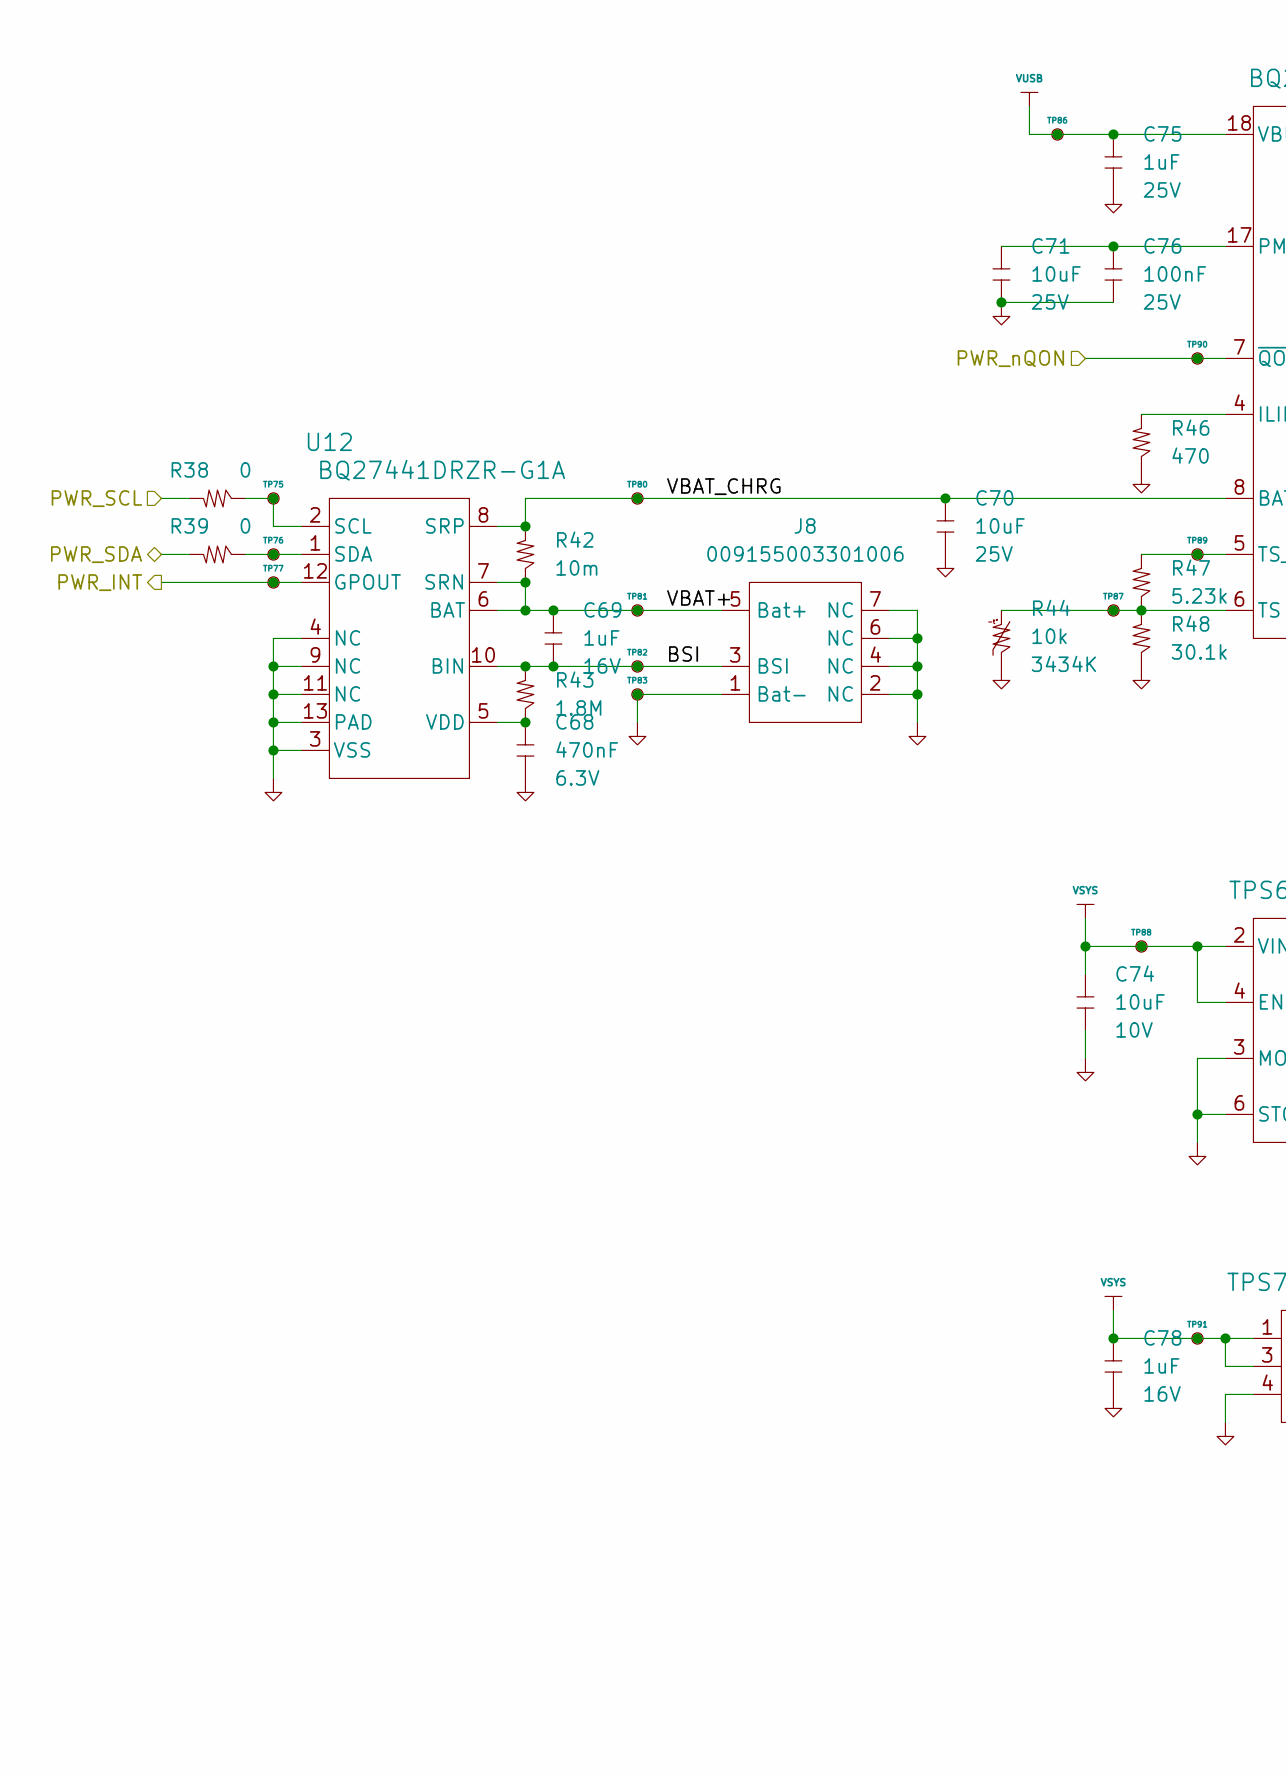
[picture p28: schematic Power.kicad_sch, part in row 1, column 1]

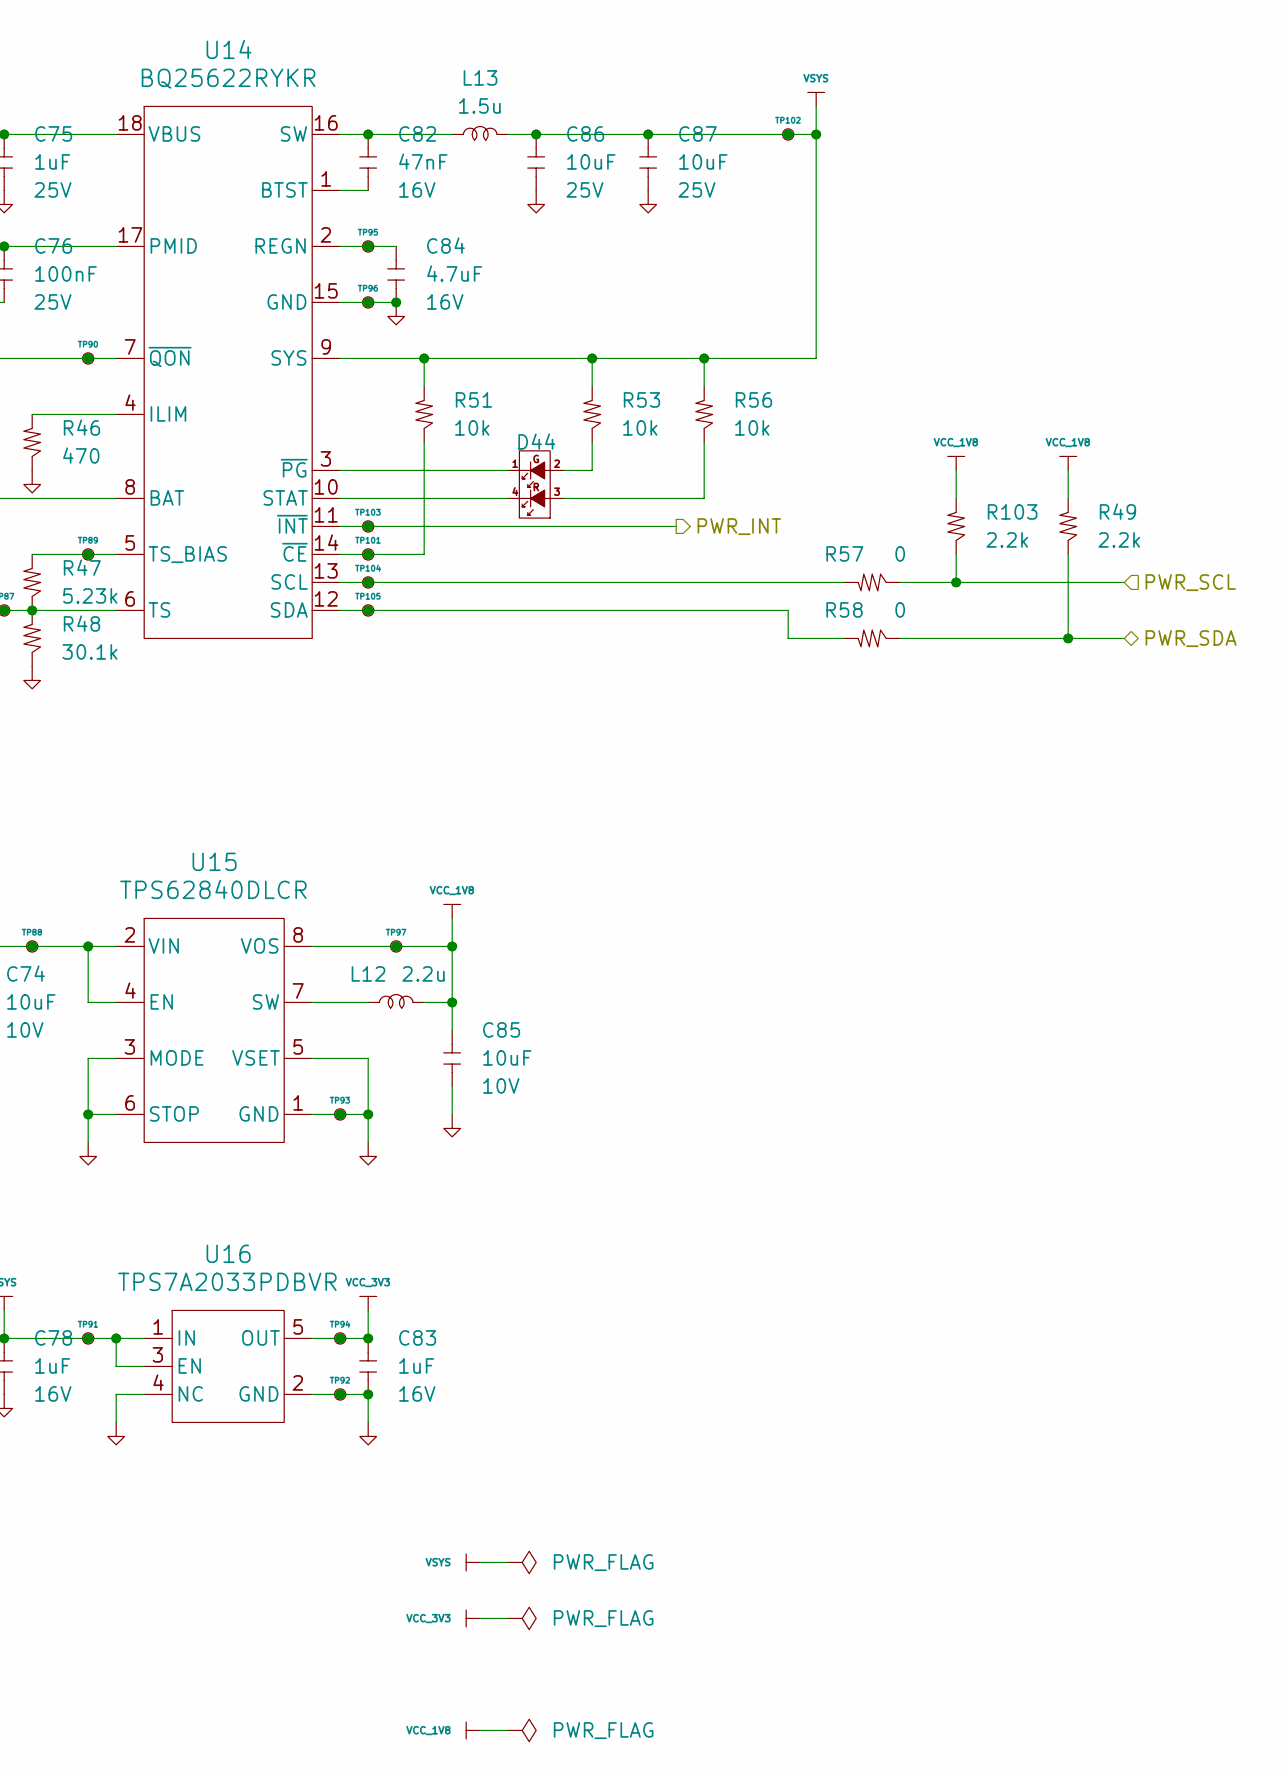
[picture p29: schematic Power.kicad_sch, part in row 1, column 2]

Parts:
C68: 470nF; C_0402_1005; Voltage 6.3V; MPN AC0402KRX5R5BB474; LCSC C3874572
C69, C78, C83: 1uF; C_0603_1608; Voltage 16V; MPN AC0603KRX7R7BB105; LCSC C3905328
C70, C71, C86, C87: 10uF; C_1206_3216; Voltage 25V; MPN CC1206KKX7R8BB106; LCSC C70462
C74, C85: 10uF; C_0603_1608; Voltage 10V; MPN CC0603KRX5R6BB106; LCSC C326057
C75: 1uF; C_1206_3216; Voltage 25V; MPN CC1206JKX7R8BB105; LCSC C541550
C76: 100nF; C_0402_1005; Voltage 25V; MPN AC0402KRX7R8BB104; LCSC C726522
C82: 47nF; C_0402_1005; Voltage 16V; MPN AC0402KPX7R7BB473; LCSC C7065820
C84: 4.7uF; C_0805_2012; Voltage 16V; MPN AC0805KKX7R7BB475; LCSC C427012
D44: LTST-C235KGKRKT; LED_LiteOn_LTST-C235KGKRKT; MPN LTST-C235KGKRKT; LCSC C125110
J8: 009155003301006; Mouser Part Number 581-009155003301006
L12: 2.2u; L_0806_2016; MPN DFE201612E-2R2M=P2; LCSC C337893
L13: 1.5u; L_1210_3225; MPN DFE322520F-1R5M; LCSC C7265122
R38, R39, R57, R58: 0; R_0402_1005; MPN AC0402FR-070RL; LCSC C226739
R42: 10m; R_0805_2012; MPN PA0805FRE470R01L; LCSC C728271
R43: 1.8M; R_0402_1005; MPN AC0402FR-071M8L; LCSC C226876
R44: 10k; R_0402_1005; MPN NCU15XH103FBSRC; LCSC C333993
R46: 470; R_0402_1005; MPN AC0402FR-7W470RL; LCSC C606172
R47: 5.23k; R_0402_1005; MPN AC0402FR-075K23L; LCSC C227154
R48: 30.1k; R_0402_1005; MPN AC0402FR-0730K1L; LCSC C226982
R49, R103: 2.2k; R_0402_1005; MPN AC0402FR-072K2L
R51, R53, R56: 10k; R_0402_1005; MPN AC0402FR-7W10KL; LCSC C850723
TP75, TP76, TP77, TP80, TP81, TP82, TP83, TP86, TP87, TP88, TP89, TP90, TP91, TP92, TP93, TP94, TP95, TP96, TP97, TP101, TP102, TP103, TP104, TP105: TestPoint_Small; TestPoint_Pad_D1.0mm; MPN test point
U12: BQ27441DRZR-G1A; DRZ0012A; MPN BQ27441DRZR-G1A; LCSC C473397
U14: BQ25622RYKR; WQFN-HR18__RYK_TEX; MPN BQ25622RYKR; LCSC C6135214
U15: TPS62840DLCR; VSON8_2P1X1P6_TEX; MPN TPS62840DLCR; LCSC C2071859
U16: TPS7A2033PDBVR; DBV0005A-IPC_C; MPN TPS7A2033PDBVR; LCSC C2862740

Connections:
BSI: C69.2, J8.3 (BSI), R43.1, TP82.1, U12.10 (BIN)
GND: C68.2, C70.2, C71.2, C74.2, C75.2, C76.2, C78.2, C83.2, C84.2, C85.2, C86.2, C87.2, J8.1 (Bat-), J8.2 (NC), J8.4 (NC), J8.6 (NC), J8.7 (NC), R44.2, R46.2, R48.2, TP83.1, TP92.1, TP93.1, TP96.1, U12.3 (VSS), U12.4 (NC), U12.9 (NC), U12.11 (NC), U12.13 (PAD), U14.15 (GND), U15.1 (GND), U15.3 (MODE), U15.5 (VSET), U15.6 (STOP), U16.2 (GND), U16.4 (NC)
unnamed: C68.1, R43.2, U12.5 (VDD)
unnamed: C71.1, C76.1, U14.17 (PMID)
unnamed: C82.1, L13.1, U14.16 (SW)
unnamed: C82.2, U14.1 (BTST)
unnamed: C84.1, TP95.1, U14.2 (REGN)
unnamed: D44.1 (K2), U14.3 (~PG)
unnamed: D44.2 (A2), R53.2
unnamed: D44.3 (A1), R56.2
unnamed: D44.4 (K1), U14.10 (STAT)
unnamed: L12.1, U15.7 (SW)
unnamed: R38.2, TP75.1, U12.2 (SCL)
unnamed: R39.2, TP76.1, U12.1 (SDA)
unnamed: R44.1, R47.2, R48.1, TP87.1, U14.6 (TS)
unnamed: R46.1, U14.4 (ILIM)
unnamed: R47.1, TP89.1, U14.5 (TS_BIAS)
unnamed: R51.2, TP101.1, U14.14 (~CE)
unnamed: R57.1, TP104.1, U14.13 (SCL)
unnamed: R58.1, TP105.1, U14.12 (SDA)
PWR_INT: TP77.1, TP103.1, U12.12 (GPOUT), U14.11 (~INT)
PWR_SCL: R38.1, R57.2, R103.2
PWR_SDA: R39.1, R49.2, R58.2
PWR_nQON: TP90.1, U14.7 (~QON)
VBAT+: C69.1, J8.5 (Bat+), R42.2, TP81.1, U12.6 (BAT), U12.7 (SRN)
VBAT_CHRG: C70.1, R42.1, TP80.1, U12.8 (SRP), U14.8 (BAT)
VCC_1V8: C85.1, L12.2, R49.1, R103.1, TP97.1, U15.8 (VOS)
VCC_3V3: C83.1, TP94.1, U16.5 (OUT)
VSYS: C74.1, C78.1, C86.1, C87.1, L13.2, R51.1, R53.1, R56.1, TP88.1, TP91.1, TP102.1, U14.9 (SYS), U15.2 (VIN), U15.4 (EN), U16.1 (IN), U16.3 (EN)
VUSB: C75.1, TP86.1, U14.18 (VBUS)
