tengigabytes/MokyaLora/hardware/kicad/SpkrAmp.kicad_sch

## KiCad design hardware/kicad/SpkrAmp.kicad_sch (2026-04-07)

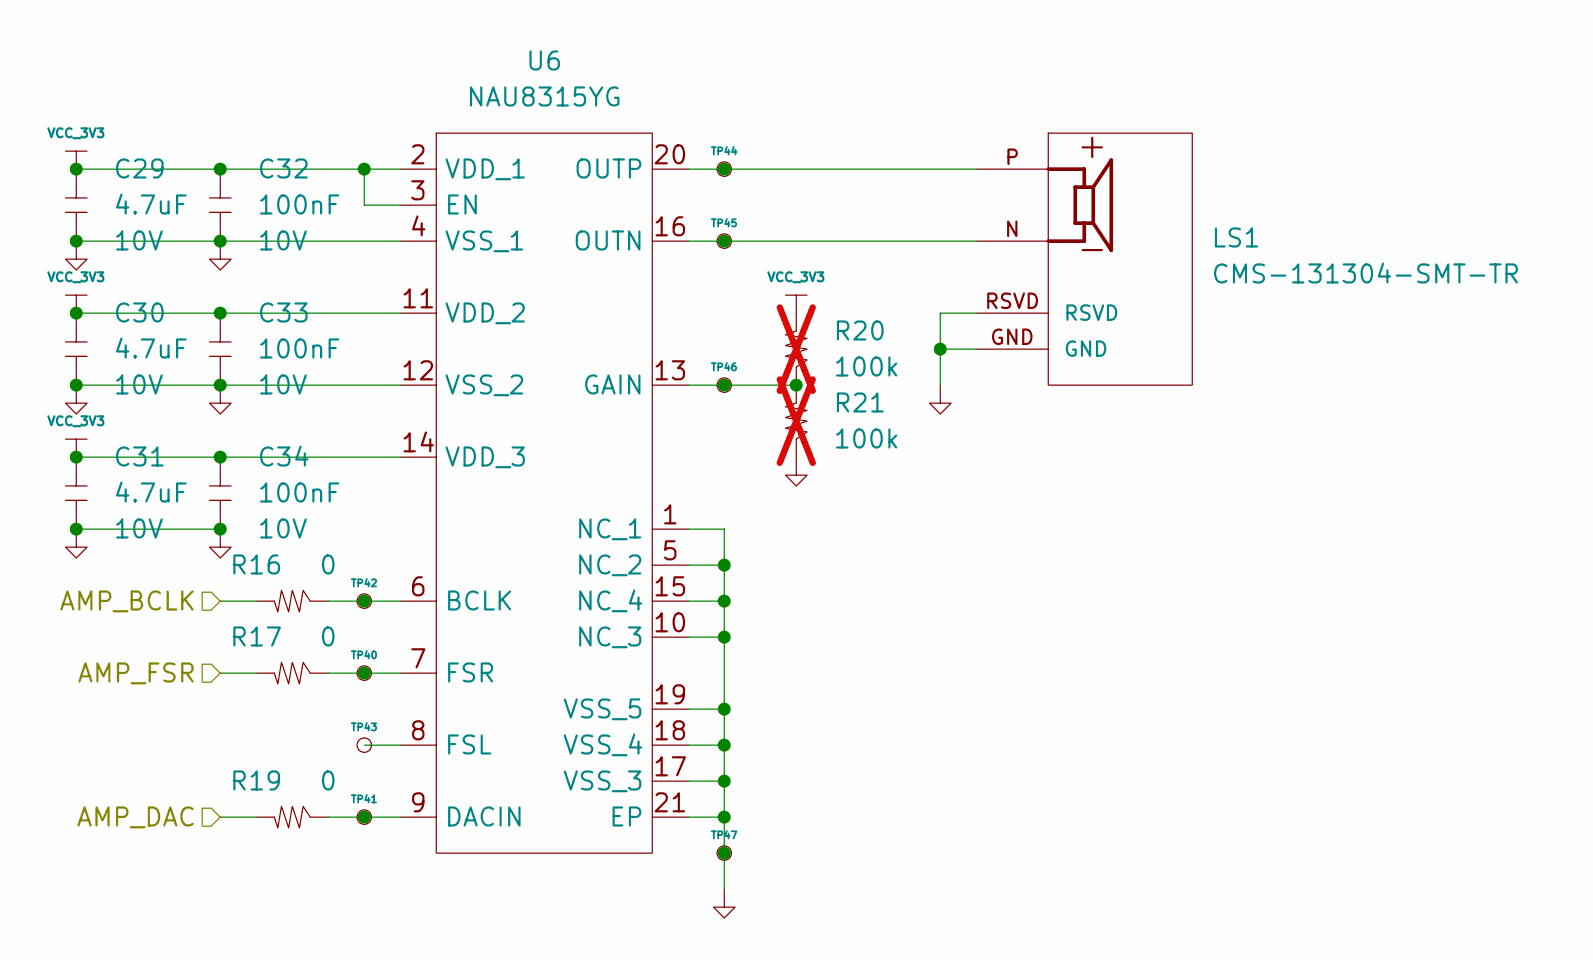
[picture p30: schematic SpkrAmp.kicad_sch]

Parts:
C29, C30, C31: 4.7uF; C_0402_1005; Voltage 10V; MPN CC0402KRX5R6BB475; LCSC C326586
C32, C33, C34: 100nF; C_0402_1005; Voltage 10V; MPN AC0402KRX7R6BB104; LCSC C3830899
LS1: CMS-131304-SMT-TR; SPKR_CMS-131304-SMT-TR; PARTREV 1.02
R16, R17, R19: 0; R_0402_1005; MPN AC0402FR-070RL; LCSC C226739
R20, R21: 100k; R_0402_1005; MPN AC0402FR-07100KL; LCSC C144809; not fitted
TP40, TP41, TP42, TP43, TP44, TP45, TP46, TP47: TestPoint_Small; TestPoint_Pad_D1.0mm; MPN test point
U6: NAU8315YG; QFN50P400X400X80-21N; Manufacturer_Part_Number NAU8315YG; LCSC C4991453

Connections:
AMP_BCLK: R16.1
AMP_DAC: R19.1
AMP_FSR: R17.1
GND: C29.2, C30.2, C31.2, C32.2, C33.2, C34.2, LS1.GND, LS1.RSVD, R21.2, TP47.1, U6.1 (NC_1), U6.4 (VSS_1), U6.5 (NC_2), U6.10 (NC_3), U6.12 (VSS_2), U6.15 (NC_4), U6.17 (VSS_3), U6.18 (VSS_4), U6.19 (VSS_5), U6.21 (EP)
unnamed: LS1.N, TP45.1, U6.16 (OUTN)
unnamed: LS1.P, TP44.1, U6.20 (OUTP)
unnamed: R16.2, TP42.1, U6.6 (BCLK)
unnamed: R17.2, TP40.1, U6.7 (FSR)
unnamed: R19.2, TP41.1, U6.9 (DACIN)
unnamed: R20.2, R21.1, TP46.1, U6.13 (GAIN)
unnamed: TP43.1, U6.8 (FSL)
VCC_3V3: C29.1, C30.1, C31.1, C32.1, C33.1, C34.1, R20.1, U6.2 (VDD_1), U6.3 (EN), U6.11 (VDD_2), U6.14 (VDD_3)
