tengigabytes/MokyaLora/hardware/kicad/VibMotor.kicad_sch

## KiCad design hardware/kicad/VibMotor.kicad_sch (2026-04-07)

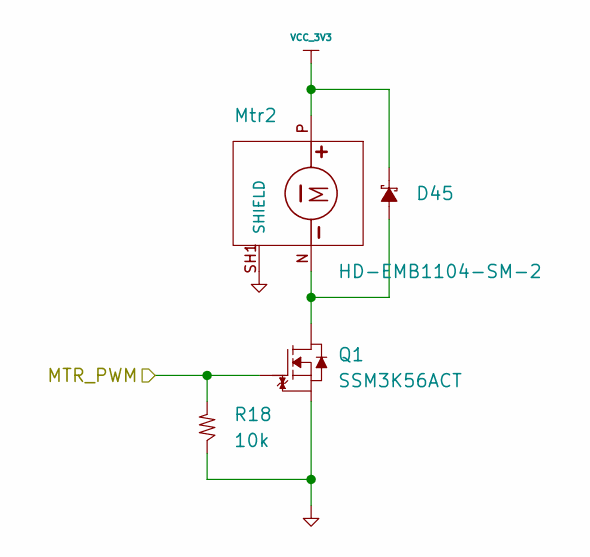
[picture p31: schematic VibMotor.kicad_sch]

Parts:
D45: D_SOD-523; MPN SDM03U40; LCSC C151333
Mtr2: HD-EMB1104-SM-2; PUI_HD-EMB1104-SM-2; MPN HD-EMB1104-SM-2
Q1: SSM3K56ACT; CST3_TOS; MPN SSM3K56ACT,L3F; LCSC C146308
R18: 10k; R_0402_1005; MPN AC0402FR-7W10KL; LCSC C850723

Connections:
GND: Mtr2.SH1 (SHIELD), Q1.2, R18.2
MTR_PWM: Q1.1, R18.1
unnamed: D45.A, Mtr2.N, Q1.3
VCC_3V3: D45.C, Mtr2.P
